ice458/RPN_Scientific_Calc/src/packs/PIC32CM2532LE00048_DFP/component/port.h

/*
 * Component description for PORT
 *
 * Copyright (c) 2023 Microchip Technology Inc. and its subsidiaries.
 *
 * Subject to your compliance with these terms, you may use Microchip software and any derivatives
 * exclusively with Microchip products. It is your responsibility to comply with third party license
 * terms applicable to your use of third party software (including open source software) that may
 * accompany Microchip software.
 *
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
 * IN NO EVENT WILL MICROCHIP BE LIABLE FOR ANY INDIRECT, SPECIAL, PUNITIVE, INCIDENTAL OR CONSEQUENTIAL
 * LOSS, DAMAGE, COST OR EXPENSE OF ANY KIND WHATSOEVER RELATED TO THE SOFTWARE, HOWEVER CAUSED, EVEN IF
 * MICROCHIP HAS BEEN ADVISED OF THE POSSIBILITY OR THE DAMAGES ARE FORESEEABLE. TO THE FULLEST EXTENT
 * ALLOWED BY LAW, MICROCHIP'S TOTAL LIABILITY ON ALL CLAIMS IN ANY WAY RELATED TO THIS SOFTWARE WILL NOT
 * EXCEED THE AMOUNT OF FEES, IF ANY, THAT YOU HAVE PAID DIRECTLY TO MICROCHIP FOR THIS SOFTWARE.
 *
 */

/* file generated from device description version 2022-09-09T06:08:26Z */
#ifndef _PIC32CMLE00_PORT_COMPONENT_H_
#define _PIC32CMLE00_PORT_COMPONENT_H_

/* ************************************************************************** */
/*   SOFTWARE API DEFINITION FOR PORT                                         */
/* ************************************************************************** */

/* -------- PORT_DIR : (PORT Offset: 0x00) (R/W 32) Data Direction -------- */
#define PORT_DIR_RESETVALUE                   _UINT32_(0x00)                                       /*  (PORT_DIR) Data Direction  Reset Value */

#define PORT_DIR_DIR_Pos                      _UINT32_(0)                                          /* (PORT_DIR) Port Data Direction Position */
#define PORT_DIR_DIR_Msk                      (_UINT32_(0xFFFFFFFF) << PORT_DIR_DIR_Pos)           /* (PORT_DIR) Port Data Direction Mask */
#define PORT_DIR_DIR(value)                   (PORT_DIR_DIR_Msk & (_UINT32_(value) << PORT_DIR_DIR_Pos)) /* Assigment of value for DIR in the PORT_DIR register */
#define PORT_DIR_Msk                          _UINT32_(0xFFFFFFFF)                                 /* (PORT_DIR) Register Mask  */


/* -------- PORT_DIRCLR : (PORT Offset: 0x04) (R/W 32) Data Direction Clear -------- */
#define PORT_DIRCLR_RESETVALUE                _UINT32_(0x00)                                       /*  (PORT_DIRCLR) Data Direction Clear  Reset Value */

#define PORT_DIRCLR_DIRCLR_Pos                _UINT32_(0)                                          /* (PORT_DIRCLR) Port Data Direction Clear Position */
#define PORT_DIRCLR_DIRCLR_Msk                (_UINT32_(0xFFFFFFFF) << PORT_DIRCLR_DIRCLR_Pos)     /* (PORT_DIRCLR) Port Data Direction Clear Mask */
#define PORT_DIRCLR_DIRCLR(value)             (PORT_DIRCLR_DIRCLR_Msk & (_UINT32_(value) << PORT_DIRCLR_DIRCLR_Pos)) /* Assigment of value for DIRCLR in the PORT_DIRCLR register */
#define PORT_DIRCLR_Msk                       _UINT32_(0xFFFFFFFF)                                 /* (PORT_DIRCLR) Register Mask  */


/* -------- PORT_DIRSET : (PORT Offset: 0x08) (R/W 32) Data Direction Set -------- */
#define PORT_DIRSET_RESETVALUE                _UINT32_(0x00)                                       /*  (PORT_DIRSET) Data Direction Set  Reset Value */

#define PORT_DIRSET_DIRSET_Pos                _UINT32_(0)                                          /* (PORT_DIRSET) Port Data Direction Set Position */
#define PORT_DIRSET_DIRSET_Msk                (_UINT32_(0xFFFFFFFF) << PORT_DIRSET_DIRSET_Pos)     /* (PORT_DIRSET) Port Data Direction Set Mask */
#define PORT_DIRSET_DIRSET(value)             (PORT_DIRSET_DIRSET_Msk & (_UINT32_(value) << PORT_DIRSET_DIRSET_Pos)) /* Assigment of value for DIRSET in the PORT_DIRSET register */
#define PORT_DIRSET_Msk                       _UINT32_(0xFFFFFFFF)                                 /* (PORT_DIRSET) Register Mask  */


/* -------- PORT_DIRTGL : (PORT Offset: 0x0C) (R/W 32) Data Direction Toggle -------- */
#define PORT_DIRTGL_RESETVALUE                _UINT32_(0x00)                                       /*  (PORT_DIRTGL) Data Direction Toggle  Reset Value */

#define PORT_DIRTGL_DIRTGL_Pos                _UINT32_(0)                                          /* (PORT_DIRTGL) Port Data Direction Toggle Position */
#define PORT_DIRTGL_DIRTGL_Msk                (_UINT32_(0xFFFFFFFF) << PORT_DIRTGL_DIRTGL_Pos)     /* (PORT_DIRTGL) Port Data Direction Toggle Mask */
#define PORT_DIRTGL_DIRTGL(value)             (PORT_DIRTGL_DIRTGL_Msk & (_UINT32_(value) << PORT_DIRTGL_DIRTGL_Pos)) /* Assigment of value for DIRTGL in the PORT_DIRTGL register */
#define PORT_DIRTGL_Msk                       _UINT32_(0xFFFFFFFF)                                 /* (PORT_DIRTGL) Register Mask  */


/* -------- PORT_OUT : (PORT Offset: 0x10) (R/W 32) Data Output Value -------- */
#define PORT_OUT_RESETVALUE                   _UINT32_(0x00)                                       /*  (PORT_OUT) Data Output Value  Reset Value */

#define PORT_OUT_OUT_Pos                      _UINT32_(0)                                          /* (PORT_OUT) PORT Data Output Value Position */
#define PORT_OUT_OUT_Msk                      (_UINT32_(0xFFFFFFFF) << PORT_OUT_OUT_Pos)           /* (PORT_OUT) PORT Data Output Value Mask */
#define PORT_OUT_OUT(value)                   (PORT_OUT_OUT_Msk & (_UINT32_(value) << PORT_OUT_OUT_Pos)) /* Assigment of value for OUT in the PORT_OUT register */
#define PORT_OUT_Msk                          _UINT32_(0xFFFFFFFF)                                 /* (PORT_OUT) Register Mask  */


/* -------- PORT_OUTCLR : (PORT Offset: 0x14) (R/W 32) Data Output Value Clear -------- */
#define PORT_OUTCLR_RESETVALUE                _UINT32_(0x00)                                       /*  (PORT_OUTCLR) Data Output Value Clear  Reset Value */

#define PORT_OUTCLR_OUTCLR_Pos                _UINT32_(0)                                          /* (PORT_OUTCLR) PORT Data Output Value Clear Position */
#define PORT_OUTCLR_OUTCLR_Msk                (_UINT32_(0xFFFFFFFF) << PORT_OUTCLR_OUTCLR_Pos)     /* (PORT_OUTCLR) PORT Data Output Value Clear Mask */
#define PORT_OUTCLR_OUTCLR(value)             (PORT_OUTCLR_OUTCLR_Msk & (_UINT32_(value) << PORT_OUTCLR_OUTCLR_Pos)) /* Assigment of value for OUTCLR in the PORT_OUTCLR register */
#define PORT_OUTCLR_Msk                       _UINT32_(0xFFFFFFFF)                                 /* (PORT_OUTCLR) Register Mask  */


/* -------- PORT_OUTSET : (PORT Offset: 0x18) (R/W 32) Data Output Value Set -------- */
#define PORT_OUTSET_RESETVALUE                _UINT32_(0x00)                                       /*  (PORT_OUTSET) Data Output Value Set  Reset Value */

#define PORT_OUTSET_OUTSET_Pos                _UINT32_(0)                                          /* (PORT_OUTSET) PORT Data Output Value Set Position */
#define PORT_OUTSET_OUTSET_Msk                (_UINT32_(0xFFFFFFFF) << PORT_OUTSET_OUTSET_Pos)     /* (PORT_OUTSET) PORT Data Output Value Set Mask */
#define PORT_OUTSET_OUTSET(value)             (PORT_OUTSET_OUTSET_Msk & (_UINT32_(value) << PORT_OUTSET_OUTSET_Pos)) /* Assigment of value for OUTSET in the PORT_OUTSET register */
#define PORT_OUTSET_Msk                       _UINT32_(0xFFFFFFFF)                                 /* (PORT_OUTSET) Register Mask  */


/* -------- PORT_OUTTGL : (PORT Offset: 0x1C) (R/W 32) Data Output Value Toggle -------- */
#define PORT_OUTTGL_RESETVALUE                _UINT32_(0x00)                                       /*  (PORT_OUTTGL) Data Output Value Toggle  Reset Value */

#define PORT_OUTTGL_OUTTGL_Pos                _UINT32_(0)                                          /* (PORT_OUTTGL) PORT Data Output Value Toggle Position */
#define PORT_OUTTGL_OUTTGL_Msk                (_UINT32_(0xFFFFFFFF) << PORT_OUTTGL_OUTTGL_Pos)     /* (PORT_OUTTGL) PORT Data Output Value Toggle Mask */
#define PORT_OUTTGL_OUTTGL(value)             (PORT_OUTTGL_OUTTGL_Msk & (_UINT32_(value) << PORT_OUTTGL_OUTTGL_Pos)) /* Assigment of value for OUTTGL in the PORT_OUTTGL register */
#define PORT_OUTTGL_Msk                       _UINT32_(0xFFFFFFFF)                                 /* (PORT_OUTTGL) Register Mask  */


/* -------- PORT_IN : (PORT Offset: 0x20) ( R/ 32) Data Input Value -------- */
#define PORT_IN_RESETVALUE                    _UINT32_(0x00)                                       /*  (PORT_IN) Data Input Value  Reset Value */

#define PORT_IN_IN_Pos                        _UINT32_(0)                                          /* (PORT_IN) PORT Data Input Value Position */
#define PORT_IN_IN_Msk                        (_UINT32_(0xFFFFFFFF) << PORT_IN_IN_Pos)             /* (PORT_IN) PORT Data Input Value Mask */
#define PORT_IN_IN(value)                     (PORT_IN_IN_Msk & (_UINT32_(value) << PORT_IN_IN_Pos)) /* Assigment of value for IN in the PORT_IN register */
#define PORT_IN_Msk                           _UINT32_(0xFFFFFFFF)                                 /* (PORT_IN) Register Mask  */


/* -------- PORT_CTRL : (PORT Offset: 0x24) (R/W 32) Control -------- */
#define PORT_CTRL_RESETVALUE                  _UINT32_(0x00)                                       /*  (PORT_CTRL) Control  Reset Value */

#define PORT_CTRL_SAMPLING_Pos                _UINT32_(0)                                          /* (PORT_CTRL) Input Sampling Mode Position */
#define PORT_CTRL_SAMPLING_Msk                (_UINT32_(0xFFFFFFFF) << PORT_CTRL_SAMPLING_Pos)     /* (PORT_CTRL) Input Sampling Mode Mask */
#define PORT_CTRL_SAMPLING(value)             (PORT_CTRL_SAMPLING_Msk & (_UINT32_(value) << PORT_CTRL_SAMPLING_Pos)) /* Assigment of value for SAMPLING in the PORT_CTRL register */
#define PORT_CTRL_Msk                         _UINT32_(0xFFFFFFFF)                                 /* (PORT_CTRL) Register Mask  */


/* -------- PORT_WRCONFIG : (PORT Offset: 0x28) ( /W 32) Write Configuration -------- */
#define PORT_WRCONFIG_RESETVALUE              _UINT32_(0x00)                                       /*  (PORT_WRCONFIG) Write Configuration  Reset Value */

#define PORT_WRCONFIG_PINMASK_Pos             _UINT32_(0)                                          /* (PORT_WRCONFIG) Pin Mask for Multiple Pin Configuration Position */
#define PORT_WRCONFIG_PINMASK_Msk             (_UINT32_(0xFFFF) << PORT_WRCONFIG_PINMASK_Pos)      /* (PORT_WRCONFIG) Pin Mask for Multiple Pin Configuration Mask */
#define PORT_WRCONFIG_PINMASK(value)          (PORT_WRCONFIG_PINMASK_Msk & (_UINT32_(value) << PORT_WRCONFIG_PINMASK_Pos)) /* Assigment of value for PINMASK in the PORT_WRCONFIG register */
#define PORT_WRCONFIG_PMUXEN_Pos              _UINT32_(16)                                         /* (PORT_WRCONFIG) Peripheral Multiplexer Enable Position */
#define PORT_WRCONFIG_PMUXEN_Msk              (_UINT32_(0x1) << PORT_WRCONFIG_PMUXEN_Pos)          /* (PORT_WRCONFIG) Peripheral Multiplexer Enable Mask */
#define PORT_WRCONFIG_PMUXEN(value)           (PORT_WRCONFIG_PMUXEN_Msk & (_UINT32_(value) << PORT_WRCONFIG_PMUXEN_Pos)) /* Assigment of value for PMUXEN in the PORT_WRCONFIG register */
#define PORT_WRCONFIG_INEN_Pos                _UINT32_(17)                                         /* (PORT_WRCONFIG) Input Enable Position */
#define PORT_WRCONFIG_INEN_Msk                (_UINT32_(0x1) << PORT_WRCONFIG_INEN_Pos)            /* (PORT_WRCONFIG) Input Enable Mask */
#define PORT_WRCONFIG_INEN(value)             (PORT_WRCONFIG_INEN_Msk & (_UINT32_(value) << PORT_WRCONFIG_INEN_Pos)) /* Assigment of value for INEN in the PORT_WRCONFIG register */
#define PORT_WRCONFIG_PULLEN_Pos              _UINT32_(18)                                         /* (PORT_WRCONFIG) Pull Enable Position */
#define PORT_WRCONFIG_PULLEN_Msk              (_UINT32_(0x1) << PORT_WRCONFIG_PULLEN_Pos)          /* (PORT_WRCONFIG) Pull Enable Mask */
#define PORT_WRCONFIG_PULLEN(value)           (PORT_WRCONFIG_PULLEN_Msk & (_UINT32_(value) << PORT_WRCONFIG_PULLEN_Pos)) /* Assigment of value for PULLEN in the PORT_WRCONFIG register */
#define PORT_WRCONFIG_DRVSTR_Pos              _UINT32_(22)                                         /* (PORT_WRCONFIG) Output Driver Strength Selection Position */
#define PORT_WRCONFIG_DRVSTR_Msk              (_UINT32_(0x1) << PORT_WRCONFIG_DRVSTR_Pos)          /* (PORT_WRCONFIG) Output Driver Strength Selection Mask */
#define PORT_WRCONFIG_DRVSTR(value)           (PORT_WRCONFIG_DRVSTR_Msk & (_UINT32_(value) << PORT_WRCONFIG_DRVSTR_Pos)) /* Assigment of value for DRVSTR in the PORT_WRCONFIG register */
#define PORT_WRCONFIG_PMUX_Pos                _UINT32_(24)                                         /* (PORT_WRCONFIG) Peripheral Multiplexing Position */
#define PORT_WRCONFIG_PMUX_Msk                (_UINT32_(0xF) << PORT_WRCONFIG_PMUX_Pos)            /* (PORT_WRCONFIG) Peripheral Multiplexing Mask */
#define PORT_WRCONFIG_PMUX(value)             (PORT_WRCONFIG_PMUX_Msk & (_UINT32_(value) << PORT_WRCONFIG_PMUX_Pos)) /* Assigment of value for PMUX in the PORT_WRCONFIG register */
#define PORT_WRCONFIG_WRPMUX_Pos              _UINT32_(28)                                         /* (PORT_WRCONFIG) Write PMUX Position */
#define PORT_WRCONFIG_WRPMUX_Msk              (_UINT32_(0x1) << PORT_WRCONFIG_WRPMUX_Pos)          /* (PORT_WRCONFIG) Write PMUX Mask */
#define PORT_WRCONFIG_WRPMUX(value)           (PORT_WRCONFIG_WRPMUX_Msk & (_UINT32_(value) << PORT_WRCONFIG_WRPMUX_Pos)) /* Assigment of value for WRPMUX in the PORT_WRCONFIG register */
#define PORT_WRCONFIG_WRPINCFG_Pos            _UINT32_(30)                                         /* (PORT_WRCONFIG) Write PINCFG Position */
#define PORT_WRCONFIG_WRPINCFG_Msk            (_UINT32_(0x1) << PORT_WRCONFIG_WRPINCFG_Pos)        /* (PORT_WRCONFIG) Write PINCFG Mask */
#define PORT_WRCONFIG_WRPINCFG(value)         (PORT_WRCONFIG_WRPINCFG_Msk & (_UINT32_(value) << PORT_WRCONFIG_WRPINCFG_Pos)) /* Assigment of value for WRPINCFG in the PORT_WRCONFIG register */
#define PORT_WRCONFIG_HWSEL_Pos               _UINT32_(31)                                         /* (PORT_WRCONFIG) Half-Word Select Position */
#define PORT_WRCONFIG_HWSEL_Msk               (_UINT32_(0x1) << PORT_WRCONFIG_HWSEL_Pos)           /* (PORT_WRCONFIG) Half-Word Select Mask */
#define PORT_WRCONFIG_HWSEL(value)            (PORT_WRCONFIG_HWSEL_Msk & (_UINT32_(value) << PORT_WRCONFIG_HWSEL_Pos)) /* Assigment of value for HWSEL in the PORT_WRCONFIG register */
#define PORT_WRCONFIG_Msk                     _UINT32_(0xDF47FFFF)                                 /* (PORT_WRCONFIG) Register Mask  */


/* -------- PORT_EVCTRL : (PORT Offset: 0x2C) (R/W 32) Event Input Control -------- */
#define PORT_EVCTRL_RESETVALUE                _UINT32_(0x00)                                       /*  (PORT_EVCTRL) Event Input Control  Reset Value */

#define PORT_EVCTRL_PID0_Pos                  _UINT32_(0)                                          /* (PORT_EVCTRL) PORT Event Pin Identifier 0 Position */
#define PORT_EVCTRL_PID0_Msk                  (_UINT32_(0x1F) << PORT_EVCTRL_PID0_Pos)             /* (PORT_EVCTRL) PORT Event Pin Identifier 0 Mask */
#define PORT_EVCTRL_PID0(value)               (PORT_EVCTRL_PID0_Msk & (_UINT32_(value) << PORT_EVCTRL_PID0_Pos)) /* Assigment of value for PID0 in the PORT_EVCTRL register */
#define PORT_EVCTRL_EVACT0_Pos                _UINT32_(5)                                          /* (PORT_EVCTRL) PORT Event Action 0 Position */
#define PORT_EVCTRL_EVACT0_Msk                (_UINT32_(0x3) << PORT_EVCTRL_EVACT0_Pos)            /* (PORT_EVCTRL) PORT Event Action 0 Mask */
#define PORT_EVCTRL_EVACT0(value)             (PORT_EVCTRL_EVACT0_Msk & (_UINT32_(value) << PORT_EVCTRL_EVACT0_Pos)) /* Assigment of value for EVACT0 in the PORT_EVCTRL register */
#define   PORT_EVCTRL_EVACT0_OUT_Val          _UINT32_(0x0)                                        /* (PORT_EVCTRL) Event output to pin  */
#define   PORT_EVCTRL_EVACT0_SET_Val          _UINT32_(0x1)                                        /* (PORT_EVCTRL) Set output register of pin on event  */
#define   PORT_EVCTRL_EVACT0_CLR_Val          _UINT32_(0x2)                                        /* (PORT_EVCTRL) Clear output register of pin on event  */
#define   PORT_EVCTRL_EVACT0_TGL_Val          _UINT32_(0x3)                                        /* (PORT_EVCTRL) Toggle output register of pin on event  */
#define PORT_EVCTRL_EVACT0_OUT                (PORT_EVCTRL_EVACT0_OUT_Val << PORT_EVCTRL_EVACT0_Pos) /* (PORT_EVCTRL) Event output to pin Position  */
#define PORT_EVCTRL_EVACT0_SET                (PORT_EVCTRL_EVACT0_SET_Val << PORT_EVCTRL_EVACT0_Pos) /* (PORT_EVCTRL) Set output register of pin on event Position  */
#define PORT_EVCTRL_EVACT0_CLR                (PORT_EVCTRL_EVACT0_CLR_Val << PORT_EVCTRL_EVACT0_Pos) /* (PORT_EVCTRL) Clear output register of pin on event Position  */
#define PORT_EVCTRL_EVACT0_TGL                (PORT_EVCTRL_EVACT0_TGL_Val << PORT_EVCTRL_EVACT0_Pos) /* (PORT_EVCTRL) Toggle output register of pin on event Position  */
#define PORT_EVCTRL_PORTEI0_Pos               _UINT32_(7)                                          /* (PORT_EVCTRL) PORT Event Input Enable 0 Position */
#define PORT_EVCTRL_PORTEI0_Msk               (_UINT32_(0x1) << PORT_EVCTRL_PORTEI0_Pos)           /* (PORT_EVCTRL) PORT Event Input Enable 0 Mask */
#define PORT_EVCTRL_PORTEI0(value)            (PORT_EVCTRL_PORTEI0_Msk & (_UINT32_(value) << PORT_EVCTRL_PORTEI0_Pos)) /* Assigment of value for PORTEI0 in the PORT_EVCTRL register */
#define PORT_EVCTRL_PID1_Pos                  _UINT32_(8)                                          /* (PORT_EVCTRL) PORT Event Pin Identifier 1 Position */
#define PORT_EVCTRL_PID1_Msk                  (_UINT32_(0x1F) << PORT_EVCTRL_PID1_Pos)             /* (PORT_EVCTRL) PORT Event Pin Identifier 1 Mask */
#define PORT_EVCTRL_PID1(value)               (PORT_EVCTRL_PID1_Msk & (_UINT32_(value) << PORT_EVCTRL_PID1_Pos)) /* Assigment of value for PID1 in the PORT_EVCTRL register */
#define PORT_EVCTRL_EVACT1_Pos                _UINT32_(13)                                         /* (PORT_EVCTRL) PORT Event Action 1 Position */
#define PORT_EVCTRL_EVACT1_Msk                (_UINT32_(0x3) << PORT_EVCTRL_EVACT1_Pos)            /* (PORT_EVCTRL) PORT Event Action 1 Mask */
#define PORT_EVCTRL_EVACT1(value)             (PORT_EVCTRL_EVACT1_Msk & (_UINT32_(value) << PORT_EVCTRL_EVACT1_Pos)) /* Assigment of value for EVACT1 in the PORT_EVCTRL register */
#define PORT_EVCTRL_PORTEI1_Pos               _UINT32_(15)                                         /* (PORT_EVCTRL) PORT Event Input Enable 1 Position */
#define PORT_EVCTRL_PORTEI1_Msk               (_UINT32_(0x1) << PORT_EVCTRL_PORTEI1_Pos)           /* (PORT_EVCTRL) PORT Event Input Enable 1 Mask */
#define PORT_EVCTRL_PORTEI1(value)            (PORT_EVCTRL_PORTEI1_Msk & (_UINT32_(value) << PORT_EVCTRL_PORTEI1_Pos)) /* Assigment of value for PORTEI1 in the PORT_EVCTRL register */
#define PORT_EVCTRL_PID2_Pos                  _UINT32_(16)                                         /* (PORT_EVCTRL) PORT Event Pin Identifier 2 Position */
#define PORT_EVCTRL_PID2_Msk                  (_UINT32_(0x1F) << PORT_EVCTRL_PID2_Pos)             /* (PORT_EVCTRL) PORT Event Pin Identifier 2 Mask */
#define PORT_EVCTRL_PID2(value)               (PORT_EVCTRL_PID2_Msk & (_UINT32_(value) << PORT_EVCTRL_PID2_Pos)) /* Assigment of value for PID2 in the PORT_EVCTRL register */
#define PORT_EVCTRL_EVACT2_Pos                _UINT32_(21)                                         /* (PORT_EVCTRL) PORT Event Action 2 Position */
#define PORT_EVCTRL_EVACT2_Msk                (_UINT32_(0x3) << PORT_EVCTRL_EVACT2_Pos)            /* (PORT_EVCTRL) PORT Event Action 2 Mask */
#define PORT_EVCTRL_EVACT2(value)             (PORT_EVCTRL_EVACT2_Msk & (_UINT32_(value) << PORT_EVCTRL_EVACT2_Pos)) /* Assigment of value for EVACT2 in the PORT_EVCTRL register */
#define PORT_EVCTRL_PORTEI2_Pos               _UINT32_(23)                                         /* (PORT_EVCTRL) PORT Event Input Enable 2 Position */
#define PORT_EVCTRL_PORTEI2_Msk               (_UINT32_(0x1) << PORT_EVCTRL_PORTEI2_Pos)           /* (PORT_EVCTRL) PORT Event Input Enable 2 Mask */
#define PORT_EVCTRL_PORTEI2(value)            (PORT_EVCTRL_PORTEI2_Msk & (_UINT32_(value) << PORT_EVCTRL_PORTEI2_Pos)) /* Assigment of value for PORTEI2 in the PORT_EVCTRL register */
#define PORT_EVCTRL_PID3_Pos                  _UINT32_(24)                                         /* (PORT_EVCTRL) PORT Event Pin Identifier 3 Position */
#define PORT_EVCTRL_PID3_Msk                  (_UINT32_(0x1F) << PORT_EVCTRL_PID3_Pos)             /* (PORT_EVCTRL) PORT Event Pin Identifier 3 Mask */
#define PORT_EVCTRL_PID3(value)               (PORT_EVCTRL_PID3_Msk & (_UINT32_(value) << PORT_EVCTRL_PID3_Pos)) /* Assigment of value for PID3 in the PORT_EVCTRL register */
#define PORT_EVCTRL_EVACT3_Pos                _UINT32_(29)                                         /* (PORT_EVCTRL) PORT Event Action 3 Position */
#define PORT_EVCTRL_EVACT3_Msk                (_UINT32_(0x3) << PORT_EVCTRL_EVACT3_Pos)            /* (PORT_EVCTRL) PORT Event Action 3 Mask */
#define PORT_EVCTRL_EVACT3(value)             (PORT_EVCTRL_EVACT3_Msk & (_UINT32_(value) << PORT_EVCTRL_EVACT3_Pos)) /* Assigment of value for EVACT3 in the PORT_EVCTRL register */
#define PORT_EVCTRL_PORTEI3_Pos               _UINT32_(31)                                         /* (PORT_EVCTRL) PORT Event Input Enable 3 Position */
#define PORT_EVCTRL_PORTEI3_Msk               (_UINT32_(0x1) << PORT_EVCTRL_PORTEI3_Pos)           /* (PORT_EVCTRL) PORT Event Input Enable 3 Mask */
#define PORT_EVCTRL_PORTEI3(value)            (PORT_EVCTRL_PORTEI3_Msk & (_UINT32_(value) << PORT_EVCTRL_PORTEI3_Pos)) /* Assigment of value for PORTEI3 in the PORT_EVCTRL register */
#define PORT_EVCTRL_Msk                       _UINT32_(0xFFFFFFFF)                                 /* (PORT_EVCTRL) Register Mask  */


/* -------- PORT_PMUX : (PORT Offset: 0x30) (R/W 8) Peripheral Multiplexing -------- */
#define PORT_PMUX_RESETVALUE                  _UINT8_(0x00)                                        /*  (PORT_PMUX) Peripheral Multiplexing  Reset Value */

#define PORT_PMUX_PMUXE_Pos                   _UINT8_(0)                                           /* (PORT_PMUX) Peripheral Multiplexing for Even-Numbered Pin Position */
#define PORT_PMUX_PMUXE_Msk                   (_UINT8_(0xF) << PORT_PMUX_PMUXE_Pos)                /* (PORT_PMUX) Peripheral Multiplexing for Even-Numbered Pin Mask */
#define PORT_PMUX_PMUXE(value)                (PORT_PMUX_PMUXE_Msk & (_UINT8_(value) << PORT_PMUX_PMUXE_Pos)) /* Assigment of value for PMUXE in the PORT_PMUX register */
#define   PORT_PMUX_PMUXE_A_Val               _UINT8_(0x0)                                         /* (PORT_PMUX) Peripheral function A selected  */
#define   PORT_PMUX_PMUXE_B_Val               _UINT8_(0x1)                                         /* (PORT_PMUX) Peripheral function B selected  */
#define   PORT_PMUX_PMUXE_C_Val               _UINT8_(0x2)                                         /* (PORT_PMUX) Peripheral function C selected  */
#define   PORT_PMUX_PMUXE_D_Val               _UINT8_(0x3)                                         /* (PORT_PMUX) Peripheral function D selected  */
#define   PORT_PMUX_PMUXE_E_Val               _UINT8_(0x4)                                         /* (PORT_PMUX) Peripheral function E selected  */
#define   PORT_PMUX_PMUXE_G_Val               _UINT8_(0x6)                                         /* (PORT_PMUX) Peripheral function G selected  */
#define   PORT_PMUX_PMUXE_H_Val               _UINT8_(0x7)                                         /* (PORT_PMUX) Peripheral function H selected  */
#define   PORT_PMUX_PMUXE_I_Val               _UINT8_(0x8)                                         /* (PORT_PMUX) Peripheral function I selected  */
#define   PORT_PMUX_PMUXE_J_Val               _UINT8_(0x9)                                         /* (PORT_PMUX) Peripheral function J selected  */
#define   PORT_PMUX_PMUXE_K_Val               _UINT8_(0xA)                                         /* (PORT_PMUX) Peripheral function K selected  */
#define PORT_PMUX_PMUXE_A                     (PORT_PMUX_PMUXE_A_Val << PORT_PMUX_PMUXE_Pos)       /* (PORT_PMUX) Peripheral function A selected Position  */
#define PORT_PMUX_PMUXE_B                     (PORT_PMUX_PMUXE_B_Val << PORT_PMUX_PMUXE_Pos)       /* (PORT_PMUX) Peripheral function B selected Position  */
#define PORT_PMUX_PMUXE_C                     (PORT_PMUX_PMUXE_C_Val << PORT_PMUX_PMUXE_Pos)       /* (PORT_PMUX) Peripheral function C selected Position  */
#define PORT_PMUX_PMUXE_D                     (PORT_PMUX_PMUXE_D_Val << PORT_PMUX_PMUXE_Pos)       /* (PORT_PMUX) Peripheral function D selected Position  */
#define PORT_PMUX_PMUXE_E                     (PORT_PMUX_PMUXE_E_Val << PORT_PMUX_PMUXE_Pos)       /* (PORT_PMUX) Peripheral function E selected Position  */
#define PORT_PMUX_PMUXE_G                     (PORT_PMUX_PMUXE_G_Val << PORT_PMUX_PMUXE_Pos)       /* (PORT_PMUX) Peripheral function G selected Position  */
#define PORT_PMUX_PMUXE_H                     (PORT_PMUX_PMUXE_H_Val << PORT_PMUX_PMUXE_Pos)       /* (PORT_PMUX) Peripheral function H selected Position  */
#define PORT_PMUX_PMUXE_I                     (PORT_PMUX_PMUXE_I_Val << PORT_PMUX_PMUXE_Pos)       /* (PORT_PMUX) Peripheral function I selected Position  */
#define PORT_PMUX_PMUXE_J                     (PORT_PMUX_PMUXE_J_Val << PORT_PMUX_PMUXE_Pos)       /* (PORT_PMUX) Peripheral function J selected Position  */
#define PORT_PMUX_PMUXE_K                     (PORT_PMUX_PMUXE_K_Val << PORT_PMUX_PMUXE_Pos)       /* (PORT_PMUX) Peripheral function K selected Position  */
#define PORT_PMUX_PMUXO_Pos                   _UINT8_(4)                                           /* (PORT_PMUX) Peripheral Multiplexing for Odd-Numbered Pin Position */
#define PORT_PMUX_PMUXO_Msk                   (_UINT8_(0xF) << PORT_PMUX_PMUXO_Pos)                /* (PORT_PMUX) Peripheral Multiplexing for Odd-Numbered Pin Mask */
#define PORT_PMUX_PMUXO(value)                (PORT_PMUX_PMUXO_Msk & (_UINT8_(value) << PORT_PMUX_PMUXO_Pos)) /* Assigment of value for PMUXO in the PORT_PMUX register */
#define   PORT_PMUX_PMUXO_A_Val               _UINT8_(0x0)                                         /* (PORT_PMUX) Peripheral function A selected  */
#define   PORT_PMUX_PMUXO_B_Val               _UINT8_(0x1)                                         /* (PORT_PMUX) Peripheral function B selected  */
#define   PORT_PMUX_PMUXO_C_Val               _UINT8_(0x2)                                         /* (PORT_PMUX) Peripheral function C selected  */
#define   PORT_PMUX_PMUXO_D_Val               _UINT8_(0x3)                                         /* (PORT_PMUX) Peripheral function D selected  */
#define   PORT_PMUX_PMUXO_E_Val               _UINT8_(0x4)                                         /* (PORT_PMUX) Peripheral function E selected  */
#define   PORT_PMUX_PMUXO_G_Val               _UINT8_(0x6)                                         /* (PORT_PMUX) Peripheral function G selected  */
#define   PORT_PMUX_PMUXO_H_Val               _UINT8_(0x7)                                         /* (PORT_PMUX) Peripheral function H selected  */
#define   PORT_PMUX_PMUXO_I_Val               _UINT8_(0x8)                                         /* (PORT_PMUX) Peripheral function I selected  */
#define   PORT_PMUX_PMUXO_J_Val               _UINT8_(0x9)                                         /* (PORT_PMUX) Peripheral function J selected  */
#define   PORT_PMUX_PMUXO_K_Val               _UINT8_(0xA)                                         /* (PORT_PMUX) Peripheral function K selected  */
#define PORT_PMUX_PMUXO_A                     (PORT_PMUX_PMUXO_A_Val << PORT_PMUX_PMUXO_Pos)       /* (PORT_PMUX) Peripheral function A selected Position  */
#define PORT_PMUX_PMUXO_B                     (PORT_PMUX_PMUXO_B_Val << PORT_PMUX_PMUXO_Pos)       /* (PORT_PMUX) Peripheral function B selected Position  */
#define PORT_PMUX_PMUXO_C                     (PORT_PMUX_PMUXO_C_Val << PORT_PMUX_PMUXO_Pos)       /* (PORT_PMUX) Peripheral function C selected Position  */
#define PORT_PMUX_PMUXO_D                     (PORT_PMUX_PMUXO_D_Val << PORT_PMUX_PMUXO_Pos)       /* (PORT_PMUX) Peripheral function D selected Position  */
#define PORT_PMUX_PMUXO_E                     (PORT_PMUX_PMUXO_E_Val << PORT_PMUX_PMUXO_Pos)       /* (PORT_PMUX) Peripheral function E selected Position  */
#define PORT_PMUX_PMUXO_G                     (PORT_PMUX_PMUXO_G_Val << PORT_PMUX_PMUXO_Pos)       /* (PORT_PMUX) Peripheral function G selected Position  */
#define PORT_PMUX_PMUXO_H                     (PORT_PMUX_PMUXO_H_Val << PORT_PMUX_PMUXO_Pos)       /* (PORT_PMUX) Peripheral function H selected Position  */
#define PORT_PMUX_PMUXO_I                     (PORT_PMUX_PMUXO_I_Val << PORT_PMUX_PMUXO_Pos)       /* (PORT_PMUX) Peripheral function I selected Position  */
#define PORT_PMUX_PMUXO_J                     (PORT_PMUX_PMUXO_J_Val << PORT_PMUX_PMUXO_Pos)       /* (PORT_PMUX) Peripheral function J selected Position  */
#define PORT_PMUX_PMUXO_K                     (PORT_PMUX_PMUXO_K_Val << PORT_PMUX_PMUXO_Pos)       /* (PORT_PMUX) Peripheral function K selected Position  */
#define PORT_PMUX_Msk                         _UINT8_(0xFF)                                        /* (PORT_PMUX) Register Mask  */


/* -------- PORT_PINCFG : (PORT Offset: 0x40) (R/W 8) Pin Configuration -------- */
#define PORT_PINCFG_RESETVALUE                _UINT8_(0x00)                                        /*  (PORT_PINCFG) Pin Configuration  Reset Value */

#define PORT_PINCFG_PMUXEN_Pos                _UINT8_(0)                                           /* (PORT_PINCFG) Peripheral Multiplexer Enable Position */
#define PORT_PINCFG_PMUXEN_Msk                (_UINT8_(0x1) << PORT_PINCFG_PMUXEN_Pos)             /* (PORT_PINCFG) Peripheral Multiplexer Enable Mask */
#define PORT_PINCFG_PMUXEN(value)             (PORT_PINCFG_PMUXEN_Msk & (_UINT8_(value) << PORT_PINCFG_PMUXEN_Pos)) /* Assigment of value for PMUXEN in the PORT_PINCFG register */
#define PORT_PINCFG_INEN_Pos                  _UINT8_(1)                                           /* (PORT_PINCFG) Input Enable Position */
#define PORT_PINCFG_INEN_Msk                  (_UINT8_(0x1) << PORT_PINCFG_INEN_Pos)               /* (PORT_PINCFG) Input Enable Mask */
#define PORT_PINCFG_INEN(value)               (PORT_PINCFG_INEN_Msk & (_UINT8_(value) << PORT_PINCFG_INEN_Pos)) /* Assigment of value for INEN in the PORT_PINCFG register */
#define PORT_PINCFG_PULLEN_Pos                _UINT8_(2)                                           /* (PORT_PINCFG) Pull Enable Position */
#define PORT_PINCFG_PULLEN_Msk                (_UINT8_(0x1) << PORT_PINCFG_PULLEN_Pos)             /* (PORT_PINCFG) Pull Enable Mask */
#define PORT_PINCFG_PULLEN(value)             (PORT_PINCFG_PULLEN_Msk & (_UINT8_(value) << PORT_PINCFG_PULLEN_Pos)) /* Assigment of value for PULLEN in the PORT_PINCFG register */
#define PORT_PINCFG_DRVSTR_Pos                _UINT8_(6)                                           /* (PORT_PINCFG) Output Driver Strength Selection Position */
#define PORT_PINCFG_DRVSTR_Msk                (_UINT8_(0x1) << PORT_PINCFG_DRVSTR_Pos)             /* (PORT_PINCFG) Output Driver Strength Selection Mask */
#define PORT_PINCFG_DRVSTR(value)             (PORT_PINCFG_DRVSTR_Msk & (_UINT8_(value) << PORT_PINCFG_DRVSTR_Pos)) /* Assigment of value for DRVSTR in the PORT_PINCFG register */
#define PORT_PINCFG_Msk                       _UINT8_(0x47)                                        /* (PORT_PINCFG) Register Mask  */


/** \brief PORT register offsets definitions */
#define PORT_DIR_REG_OFST              _UINT32_(0x00)      /* (PORT_DIR) Data Direction Offset */
#define PORT_DIRCLR_REG_OFST           _UINT32_(0x04)      /* (PORT_DIRCLR) Data Direction Clear Offset */
#define PORT_DIRSET_REG_OFST           _UINT32_(0x08)      /* (PORT_DIRSET) Data Direction Set Offset */
#define PORT_DIRTGL_REG_OFST           _UINT32_(0x0C)      /* (PORT_DIRTGL) Data Direction Toggle Offset */
#define PORT_OUT_REG_OFST              _UINT32_(0x10)      /* (PORT_OUT) Data Output Value Offset */
#define PORT_OUTCLR_REG_OFST           _UINT32_(0x14)      /* (PORT_OUTCLR) Data Output Value Clear Offset */
#define PORT_OUTSET_REG_OFST           _UINT32_(0x18)      /* (PORT_OUTSET) Data Output Value Set Offset */
#define PORT_OUTTGL_REG_OFST           _UINT32_(0x1C)      /* (PORT_OUTTGL) Data Output Value Toggle Offset */
#define PORT_IN_REG_OFST               _UINT32_(0x20)      /* (PORT_IN) Data Input Value Offset */
#define PORT_CTRL_REG_OFST             _UINT32_(0x24)      /* (PORT_CTRL) Control Offset */
#define PORT_WRCONFIG_REG_OFST         _UINT32_(0x28)      /* (PORT_WRCONFIG) Write Configuration Offset */
#define PORT_EVCTRL_REG_OFST           _UINT32_(0x2C)      /* (PORT_EVCTRL) Event Input Control Offset */
#define PORT_PMUX_REG_OFST             _UINT32_(0x30)      /* (PORT_PMUX) Peripheral Multiplexing Offset */
#define PORT_PMUX0_REG_OFST            _UINT32_(0x30)      /* (PORT_PMUX0) Peripheral Multiplexing Offset */
#define PORT_PMUX1_REG_OFST            _UINT32_(0x31)      /* (PORT_PMUX1) Peripheral Multiplexing Offset */
#define PORT_PMUX2_REG_OFST            _UINT32_(0x32)      /* (PORT_PMUX2) Peripheral Multiplexing Offset */
#define PORT_PMUX3_REG_OFST            _UINT32_(0x33)      /* (PORT_PMUX3) Peripheral Multiplexing Offset */
#define PORT_PMUX4_REG_OFST            _UINT32_(0x34)      /* (PORT_PMUX4) Peripheral Multiplexing Offset */
#define PORT_PMUX5_REG_OFST            _UINT32_(0x35)      /* (PORT_PMUX5) Peripheral Multiplexing Offset */
#define PORT_PMUX6_REG_OFST            _UINT32_(0x36)      /* (PORT_PMUX6) Peripheral Multiplexing Offset */
#define PORT_PMUX7_REG_OFST            _UINT32_(0x37)      /* (PORT_PMUX7) Peripheral Multiplexing Offset */
#define PORT_PMUX8_REG_OFST            _UINT32_(0x38)      /* (PORT_PMUX8) Peripheral Multiplexing Offset */
#define PORT_PMUX9_REG_OFST            _UINT32_(0x39)      /* (PORT_PMUX9) Peripheral Multiplexing Offset */
#define PORT_PMUX10_REG_OFST           _UINT32_(0x3A)      /* (PORT_PMUX10) Peripheral Multiplexing Offset */
#define PORT_PMUX11_REG_OFST           _UINT32_(0x3B)      /* (PORT_PMUX11) Peripheral Multiplexing Offset */
#define PORT_PMUX12_REG_OFST           _UINT32_(0x3C)      /* (PORT_PMUX12) Peripheral Multiplexing Offset */
#define PORT_PMUX13_REG_OFST           _UINT32_(0x3D)      /* (PORT_PMUX13) Peripheral Multiplexing Offset */
#define PORT_PMUX14_REG_OFST           _UINT32_(0x3E)      /* (PORT_PMUX14) Peripheral Multiplexing Offset */
#define PORT_PMUX15_REG_OFST           _UINT32_(0x3F)      /* (PORT_PMUX15) Peripheral Multiplexing Offset */
#define PORT_PINCFG_REG_OFST           _UINT32_(0x40)      /* (PORT_PINCFG) Pin Configuration Offset */
#define PORT_PINCFG0_REG_OFST          _UINT32_(0x40)      /* (PORT_PINCFG0) Pin Configuration Offset */
#define PORT_PINCFG1_REG_OFST          _UINT32_(0x41)      /* (PORT_PINCFG1) Pin Configuration Offset */
#define PORT_PINCFG2_REG_OFST          _UINT32_(0x42)      /* (PORT_PINCFG2) Pin Configuration Offset */
#define PORT_PINCFG3_REG_OFST          _UINT32_(0x43)      /* (PORT_PINCFG3) Pin Configuration Offset */
#define PORT_PINCFG4_REG_OFST          _UINT32_(0x44)      /* (PORT_PINCFG4) Pin Configuration Offset */
#define PORT_PINCFG5_REG_OFST          _UINT32_(0x45)      /* (PORT_PINCFG5) Pin Configuration Offset */
#define PORT_PINCFG6_REG_OFST          _UINT32_(0x46)      /* (PORT_PINCFG6) Pin Configuration Offset */
#define PORT_PINCFG7_REG_OFST          _UINT32_(0x47)      /* (PORT_PINCFG7) Pin Configuration Offset */
#define PORT_PINCFG8_REG_OFST          _UINT32_(0x48)      /* (PORT_PINCFG8) Pin Configuration Offset */
#define PORT_PINCFG9_REG_OFST          _UINT32_(0x49)      /* (PORT_PINCFG9) Pin Configuration Offset */
#define PORT_PINCFG10_REG_OFST         _UINT32_(0x4A)      /* (PORT_PINCFG10) Pin Configuration Offset */
#define PORT_PINCFG11_REG_OFST         _UINT32_(0x4B)      /* (PORT_PINCFG11) Pin Configuration Offset */
#define PORT_PINCFG12_REG_OFST         _UINT32_(0x4C)      /* (PORT_PINCFG12) Pin Configuration Offset */
#define PORT_PINCFG13_REG_OFST         _UINT32_(0x4D)      /* (PORT_PINCFG13) Pin Configuration Offset */
#define PORT_PINCFG14_REG_OFST         _UINT32_(0x4E)      /* (PORT_PINCFG14) Pin Configuration Offset */
#define PORT_PINCFG15_REG_OFST         _UINT32_(0x4F)      /* (PORT_PINCFG15) Pin Configuration Offset */
#define PORT_PINCFG16_REG_OFST         _UINT32_(0x50)      /* (PORT_PINCFG16) Pin Configuration Offset */
#define PORT_PINCFG17_REG_OFST         _UINT32_(0x51)      /* (PORT_PINCFG17) Pin Configuration Offset */
#define PORT_PINCFG18_REG_OFST         _UINT32_(0x52)      /* (PORT_PINCFG18) Pin Configuration Offset */
#define PORT_PINCFG19_REG_OFST         _UINT32_(0x53)      /* (PORT_PINCFG19) Pin Configuration Offset */
#define PORT_PINCFG20_REG_OFST         _UINT32_(0x54)      /* (PORT_PINCFG20) Pin Configuration Offset */
#define PORT_PINCFG21_REG_OFST         _UINT32_(0x55)      /* (PORT_PINCFG21) Pin Configuration Offset */
#define PORT_PINCFG22_REG_OFST         _UINT32_(0x56)      /* (PORT_PINCFG22) Pin Configuration Offset */
#define PORT_PINCFG23_REG_OFST         _UINT32_(0x57)      /* (PORT_PINCFG23) Pin Configuration Offset */
#define PORT_PINCFG24_REG_OFST         _UINT32_(0x58)      /* (PORT_PINCFG24) Pin Configuration Offset */
#define PORT_PINCFG25_REG_OFST         _UINT32_(0x59)      /* (PORT_PINCFG25) Pin Configuration Offset */
#define PORT_PINCFG26_REG_OFST         _UINT32_(0x5A)      /* (PORT_PINCFG26) Pin Configuration Offset */
#define PORT_PINCFG27_REG_OFST         _UINT32_(0x5B)      /* (PORT_PINCFG27) Pin Configuration Offset */
#define PORT_PINCFG28_REG_OFST         _UINT32_(0x5C)      /* (PORT_PINCFG28) Pin Configuration Offset */
#define PORT_PINCFG29_REG_OFST         _UINT32_(0x5D)      /* (PORT_PINCFG29) Pin Configuration Offset */
#define PORT_PINCFG30_REG_OFST         _UINT32_(0x5E)      /* (PORT_PINCFG30) Pin Configuration Offset */
#define PORT_PINCFG31_REG_OFST         _UINT32_(0x5F)      /* (PORT_PINCFG31) Pin Configuration Offset */

#if !(defined(__ASSEMBLER__) || defined(__IAR_SYSTEMS_ASM__))
/** \brief GROUP register API structure */
typedef struct
{
  __IO  uint32_t                       PORT_DIR;           /**< Offset: 0x00 (R/W  32) Data Direction */
  __IO  uint32_t                       PORT_DIRCLR;        /**< Offset: 0x04 (R/W  32) Data Direction Clear */
  __IO  uint32_t                       PORT_DIRSET;        /**< Offset: 0x08 (R/W  32) Data Direction Set */
  __IO  uint32_t                       PORT_DIRTGL;        /**< Offset: 0x0C (R/W  32) Data Direction Toggle */
  __IO  uint32_t                       PORT_OUT;           /**< Offset: 0x10 (R/W  32) Data Output Value */
  __IO  uint32_t                       PORT_OUTCLR;        /**< Offset: 0x14 (R/W  32) Data Output Value Clear */
  __IO  uint32_t                       PORT_OUTSET;        /**< Offset: 0x18 (R/W  32) Data Output Value Set */
  __IO  uint32_t                       PORT_OUTTGL;        /**< Offset: 0x1C (R/W  32) Data Output Value Toggle */
  __I   uint32_t                       PORT_IN;            /**< Offset: 0x20 (R/   32) Data Input Value */
  __IO  uint32_t                       PORT_CTRL;          /**< Offset: 0x24 (R/W  32) Control */
  __O   uint32_t                       PORT_WRCONFIG;      /**< Offset: 0x28 ( /W  32) Write Configuration */
  __IO  uint32_t                       PORT_EVCTRL;        /**< Offset: 0x2C (R/W  32) Event Input Control */
  __IO  uint8_t                        PORT_PMUX[16];      /**< Offset: 0x30 (R/W  8) Peripheral Multiplexing */
  __IO  uint8_t                        PORT_PINCFG[32];    /**< Offset: 0x40 (R/W  8) Pin Configuration */
  __I   uint8_t                        Reserved1[0x20];
} port_group_registers_t;

#define PORT_GROUP_NUMBER 3

/** \brief PORT register API structure */
typedef struct
{  /* Port Module */
        port_group_registers_t         GROUP[PORT_GROUP_NUMBER]; /**< Offset: 0x00  */
} port_registers_t;


#endif /* !(defined(__ASSEMBLER__) || defined(__IAR_SYSTEMS_ASM__)) */
#endif /* _PIC32CMLE00_PORT_COMPONENT_H_ */
