ice458/RPN_Scientific_Calc/src/packs/PIC32CM2532LE00048_DFP/component/ac.h

/*
 * Component description for AC
 *
 * Copyright (c) 2023 Microchip Technology Inc. and its subsidiaries.
 *
 * Subject to your compliance with these terms, you may use Microchip software and any derivatives
 * exclusively with Microchip products. It is your responsibility to comply with third party license
 * terms applicable to your use of third party software (including open source software) that may
 * accompany Microchip software.
 *
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
 * IN NO EVENT WILL MICROCHIP BE LIABLE FOR ANY INDIRECT, SPECIAL, PUNITIVE, INCIDENTAL OR CONSEQUENTIAL
 * LOSS, DAMAGE, COST OR EXPENSE OF ANY KIND WHATSOEVER RELATED TO THE SOFTWARE, HOWEVER CAUSED, EVEN IF
 * MICROCHIP HAS BEEN ADVISED OF THE POSSIBILITY OR THE DAMAGES ARE FORESEEABLE. TO THE FULLEST EXTENT
 * ALLOWED BY LAW, MICROCHIP'S TOTAL LIABILITY ON ALL CLAIMS IN ANY WAY RELATED TO THIS SOFTWARE WILL NOT
 * EXCEED THE AMOUNT OF FEES, IF ANY, THAT YOU HAVE PAID DIRECTLY TO MICROCHIP FOR THIS SOFTWARE.
 *
 */

/* file generated from device description version 2022-09-09T06:08:26Z */
#ifndef _PIC32CMLE00_AC_COMPONENT_H_
#define _PIC32CMLE00_AC_COMPONENT_H_

/* ************************************************************************** */
/*   SOFTWARE API DEFINITION FOR AC                                           */
/* ************************************************************************** */

/* -------- AC_CTRLA : (AC Offset: 0x00) (R/W 8) Control A -------- */
#define AC_CTRLA_RESETVALUE                   _UINT8_(0x00)                                        /*  (AC_CTRLA) Control A  Reset Value */

#define AC_CTRLA_SWRST_Pos                    _UINT8_(0)                                           /* (AC_CTRLA) Software Reset Position */
#define AC_CTRLA_SWRST_Msk                    (_UINT8_(0x1) << AC_CTRLA_SWRST_Pos)                 /* (AC_CTRLA) Software Reset Mask */
#define AC_CTRLA_SWRST(value)                 (AC_CTRLA_SWRST_Msk & (_UINT8_(value) << AC_CTRLA_SWRST_Pos)) /* Assigment of value for SWRST in the AC_CTRLA register */
#define AC_CTRLA_ENABLE_Pos                   _UINT8_(1)                                           /* (AC_CTRLA) Enable Position */
#define AC_CTRLA_ENABLE_Msk                   (_UINT8_(0x1) << AC_CTRLA_ENABLE_Pos)                /* (AC_CTRLA) Enable Mask */
#define AC_CTRLA_ENABLE(value)                (AC_CTRLA_ENABLE_Msk & (_UINT8_(value) << AC_CTRLA_ENABLE_Pos)) /* Assigment of value for ENABLE in the AC_CTRLA register */
#define AC_CTRLA_Msk                          _UINT8_(0x03)                                        /* (AC_CTRLA) Register Mask  */


/* -------- AC_CTRLB : (AC Offset: 0x01) (R/W 8) Control B -------- */
#define AC_CTRLB_RESETVALUE                   _UINT8_(0x00)                                        /*  (AC_CTRLB) Control B  Reset Value */

#define AC_CTRLB_START0_Pos                   _UINT8_(0)                                           /* (AC_CTRLB) Comparator 0 Start Comparison Position */
#define AC_CTRLB_START0_Msk                   (_UINT8_(0x1) << AC_CTRLB_START0_Pos)                /* (AC_CTRLB) Comparator 0 Start Comparison Mask */
#define AC_CTRLB_START0(value)                (AC_CTRLB_START0_Msk & (_UINT8_(value) << AC_CTRLB_START0_Pos)) /* Assigment of value for START0 in the AC_CTRLB register */
#define AC_CTRLB_START1_Pos                   _UINT8_(1)                                           /* (AC_CTRLB) Comparator 1 Start Comparison Position */
#define AC_CTRLB_START1_Msk                   (_UINT8_(0x1) << AC_CTRLB_START1_Pos)                /* (AC_CTRLB) Comparator 1 Start Comparison Mask */
#define AC_CTRLB_START1(value)                (AC_CTRLB_START1_Msk & (_UINT8_(value) << AC_CTRLB_START1_Pos)) /* Assigment of value for START1 in the AC_CTRLB register */
#define AC_CTRLB_START2_Pos                   _UINT8_(2)                                           /* (AC_CTRLB) Comparator 2 Start Comparison Position */
#define AC_CTRLB_START2_Msk                   (_UINT8_(0x1) << AC_CTRLB_START2_Pos)                /* (AC_CTRLB) Comparator 2 Start Comparison Mask */
#define AC_CTRLB_START2(value)                (AC_CTRLB_START2_Msk & (_UINT8_(value) << AC_CTRLB_START2_Pos)) /* Assigment of value for START2 in the AC_CTRLB register */
#define AC_CTRLB_START3_Pos                   _UINT8_(3)                                           /* (AC_CTRLB) Comparator 3 Start Comparison Position */
#define AC_CTRLB_START3_Msk                   (_UINT8_(0x1) << AC_CTRLB_START3_Pos)                /* (AC_CTRLB) Comparator 3 Start Comparison Mask */
#define AC_CTRLB_START3(value)                (AC_CTRLB_START3_Msk & (_UINT8_(value) << AC_CTRLB_START3_Pos)) /* Assigment of value for START3 in the AC_CTRLB register */
#define AC_CTRLB_Msk                          _UINT8_(0x0F)                                        /* (AC_CTRLB) Register Mask  */

#define AC_CTRLB_START_Pos                    _UINT8_(0)                                           /* (AC_CTRLB Position) Comparator 3 Start Comparison */
#define AC_CTRLB_START_Msk                    (_UINT8_(0xF) << AC_CTRLB_START_Pos)                 /* (AC_CTRLB Mask) START */
#define AC_CTRLB_START(value)                 (AC_CTRLB_START_Msk & (_UINT8_(value) << AC_CTRLB_START_Pos)) 

/* -------- AC_EVCTRL : (AC Offset: 0x02) (R/W 16) Event Control -------- */
#define AC_EVCTRL_RESETVALUE                  _UINT16_(0x00)                                       /*  (AC_EVCTRL) Event Control  Reset Value */

#define AC_EVCTRL_COMPEO0_Pos                 _UINT16_(0)                                          /* (AC_EVCTRL) Comparator 0 Event Output Enable Position */
#define AC_EVCTRL_COMPEO0_Msk                 (_UINT16_(0x1) << AC_EVCTRL_COMPEO0_Pos)             /* (AC_EVCTRL) Comparator 0 Event Output Enable Mask */
#define AC_EVCTRL_COMPEO0(value)              (AC_EVCTRL_COMPEO0_Msk & (_UINT16_(value) << AC_EVCTRL_COMPEO0_Pos)) /* Assigment of value for COMPEO0 in the AC_EVCTRL register */
#define AC_EVCTRL_COMPEO1_Pos                 _UINT16_(1)                                          /* (AC_EVCTRL) Comparator 1 Event Output Enable Position */
#define AC_EVCTRL_COMPEO1_Msk                 (_UINT16_(0x1) << AC_EVCTRL_COMPEO1_Pos)             /* (AC_EVCTRL) Comparator 1 Event Output Enable Mask */
#define AC_EVCTRL_COMPEO1(value)              (AC_EVCTRL_COMPEO1_Msk & (_UINT16_(value) << AC_EVCTRL_COMPEO1_Pos)) /* Assigment of value for COMPEO1 in the AC_EVCTRL register */
#define AC_EVCTRL_COMPEO2_Pos                 _UINT16_(2)                                          /* (AC_EVCTRL) Comparator 2 Event Output Enable Position */
#define AC_EVCTRL_COMPEO2_Msk                 (_UINT16_(0x1) << AC_EVCTRL_COMPEO2_Pos)             /* (AC_EVCTRL) Comparator 2 Event Output Enable Mask */
#define AC_EVCTRL_COMPEO2(value)              (AC_EVCTRL_COMPEO2_Msk & (_UINT16_(value) << AC_EVCTRL_COMPEO2_Pos)) /* Assigment of value for COMPEO2 in the AC_EVCTRL register */
#define AC_EVCTRL_COMPEO3_Pos                 _UINT16_(3)                                          /* (AC_EVCTRL) Comparator 3 Event Output Enable Position */
#define AC_EVCTRL_COMPEO3_Msk                 (_UINT16_(0x1) << AC_EVCTRL_COMPEO3_Pos)             /* (AC_EVCTRL) Comparator 3 Event Output Enable Mask */
#define AC_EVCTRL_COMPEO3(value)              (AC_EVCTRL_COMPEO3_Msk & (_UINT16_(value) << AC_EVCTRL_COMPEO3_Pos)) /* Assigment of value for COMPEO3 in the AC_EVCTRL register */
#define AC_EVCTRL_WINEO0_Pos                  _UINT16_(4)                                          /* (AC_EVCTRL) Window 0 Event Output Enable Position */
#define AC_EVCTRL_WINEO0_Msk                  (_UINT16_(0x1) << AC_EVCTRL_WINEO0_Pos)              /* (AC_EVCTRL) Window 0 Event Output Enable Mask */
#define AC_EVCTRL_WINEO0(value)               (AC_EVCTRL_WINEO0_Msk & (_UINT16_(value) << AC_EVCTRL_WINEO0_Pos)) /* Assigment of value for WINEO0 in the AC_EVCTRL register */
#define AC_EVCTRL_WINEO1_Pos                  _UINT16_(5)                                          /* (AC_EVCTRL) Window 1 Event Output Enable Position */
#define AC_EVCTRL_WINEO1_Msk                  (_UINT16_(0x1) << AC_EVCTRL_WINEO1_Pos)              /* (AC_EVCTRL) Window 1 Event Output Enable Mask */
#define AC_EVCTRL_WINEO1(value)               (AC_EVCTRL_WINEO1_Msk & (_UINT16_(value) << AC_EVCTRL_WINEO1_Pos)) /* Assigment of value for WINEO1 in the AC_EVCTRL register */
#define AC_EVCTRL_COMPEI0_Pos                 _UINT16_(8)                                          /* (AC_EVCTRL) Comparator 0 Event Input Enable Position */
#define AC_EVCTRL_COMPEI0_Msk                 (_UINT16_(0x1) << AC_EVCTRL_COMPEI0_Pos)             /* (AC_EVCTRL) Comparator 0 Event Input Enable Mask */
#define AC_EVCTRL_COMPEI0(value)              (AC_EVCTRL_COMPEI0_Msk & (_UINT16_(value) << AC_EVCTRL_COMPEI0_Pos)) /* Assigment of value for COMPEI0 in the AC_EVCTRL register */
#define AC_EVCTRL_COMPEI1_Pos                 _UINT16_(9)                                          /* (AC_EVCTRL) Comparator 1 Event Input Enable Position */
#define AC_EVCTRL_COMPEI1_Msk                 (_UINT16_(0x1) << AC_EVCTRL_COMPEI1_Pos)             /* (AC_EVCTRL) Comparator 1 Event Input Enable Mask */
#define AC_EVCTRL_COMPEI1(value)              (AC_EVCTRL_COMPEI1_Msk & (_UINT16_(value) << AC_EVCTRL_COMPEI1_Pos)) /* Assigment of value for COMPEI1 in the AC_EVCTRL register */
#define AC_EVCTRL_COMPEI2_Pos                 _UINT16_(10)                                         /* (AC_EVCTRL) Comparator 2 Event Input Enable Position */
#define AC_EVCTRL_COMPEI2_Msk                 (_UINT16_(0x1) << AC_EVCTRL_COMPEI2_Pos)             /* (AC_EVCTRL) Comparator 2 Event Input Enable Mask */
#define AC_EVCTRL_COMPEI2(value)              (AC_EVCTRL_COMPEI2_Msk & (_UINT16_(value) << AC_EVCTRL_COMPEI2_Pos)) /* Assigment of value for COMPEI2 in the AC_EVCTRL register */
#define AC_EVCTRL_COMPEI3_Pos                 _UINT16_(11)                                         /* (AC_EVCTRL) Comparator 3 Event Input Enable Position */
#define AC_EVCTRL_COMPEI3_Msk                 (_UINT16_(0x1) << AC_EVCTRL_COMPEI3_Pos)             /* (AC_EVCTRL) Comparator 3 Event Input Enable Mask */
#define AC_EVCTRL_COMPEI3(value)              (AC_EVCTRL_COMPEI3_Msk & (_UINT16_(value) << AC_EVCTRL_COMPEI3_Pos)) /* Assigment of value for COMPEI3 in the AC_EVCTRL register */
#define AC_EVCTRL_INVEI0_Pos                  _UINT16_(12)                                         /* (AC_EVCTRL) Comparator 0 Input Event Invert Enable Position */
#define AC_EVCTRL_INVEI0_Msk                  (_UINT16_(0x1) << AC_EVCTRL_INVEI0_Pos)              /* (AC_EVCTRL) Comparator 0 Input Event Invert Enable Mask */
#define AC_EVCTRL_INVEI0(value)               (AC_EVCTRL_INVEI0_Msk & (_UINT16_(value) << AC_EVCTRL_INVEI0_Pos)) /* Assigment of value for INVEI0 in the AC_EVCTRL register */
#define AC_EVCTRL_INVEI1_Pos                  _UINT16_(13)                                         /* (AC_EVCTRL) Comparator 1 Input Event Invert Enable Position */
#define AC_EVCTRL_INVEI1_Msk                  (_UINT16_(0x1) << AC_EVCTRL_INVEI1_Pos)              /* (AC_EVCTRL) Comparator 1 Input Event Invert Enable Mask */
#define AC_EVCTRL_INVEI1(value)               (AC_EVCTRL_INVEI1_Msk & (_UINT16_(value) << AC_EVCTRL_INVEI1_Pos)) /* Assigment of value for INVEI1 in the AC_EVCTRL register */
#define AC_EVCTRL_INVEI2_Pos                  _UINT16_(14)                                         /* (AC_EVCTRL) Comparator 2 Input Event Invert Enable Position */
#define AC_EVCTRL_INVEI2_Msk                  (_UINT16_(0x1) << AC_EVCTRL_INVEI2_Pos)              /* (AC_EVCTRL) Comparator 2 Input Event Invert Enable Mask */
#define AC_EVCTRL_INVEI2(value)               (AC_EVCTRL_INVEI2_Msk & (_UINT16_(value) << AC_EVCTRL_INVEI2_Pos)) /* Assigment of value for INVEI2 in the AC_EVCTRL register */
#define AC_EVCTRL_INVEI3_Pos                  _UINT16_(15)                                         /* (AC_EVCTRL) Comparator 3 Input Event Invert Enable Position */
#define AC_EVCTRL_INVEI3_Msk                  (_UINT16_(0x1) << AC_EVCTRL_INVEI3_Pos)              /* (AC_EVCTRL) Comparator 3 Input Event Invert Enable Mask */
#define AC_EVCTRL_INVEI3(value)               (AC_EVCTRL_INVEI3_Msk & (_UINT16_(value) << AC_EVCTRL_INVEI3_Pos)) /* Assigment of value for INVEI3 in the AC_EVCTRL register */
#define AC_EVCTRL_Msk                         _UINT16_(0xFF3F)                                     /* (AC_EVCTRL) Register Mask  */

#define AC_EVCTRL_COMPEO_Pos                  _UINT16_(0)                                          /* (AC_EVCTRL Position) Comparator x Event Output Enable */
#define AC_EVCTRL_COMPEO_Msk                  (_UINT16_(0xF) << AC_EVCTRL_COMPEO_Pos)              /* (AC_EVCTRL Mask) COMPEO */
#define AC_EVCTRL_COMPEO(value)               (AC_EVCTRL_COMPEO_Msk & (_UINT16_(value) << AC_EVCTRL_COMPEO_Pos)) 
#define AC_EVCTRL_WINEO_Pos                   _UINT16_(4)                                          /* (AC_EVCTRL Position) Window x Event Output Enable */
#define AC_EVCTRL_WINEO_Msk                   (_UINT16_(0x3) << AC_EVCTRL_WINEO_Pos)               /* (AC_EVCTRL Mask) WINEO */
#define AC_EVCTRL_WINEO(value)                (AC_EVCTRL_WINEO_Msk & (_UINT16_(value) << AC_EVCTRL_WINEO_Pos)) 
#define AC_EVCTRL_COMPEI_Pos                  _UINT16_(8)                                          /* (AC_EVCTRL Position) Comparator x Event Input Enable */
#define AC_EVCTRL_COMPEI_Msk                  (_UINT16_(0xF) << AC_EVCTRL_COMPEI_Pos)              /* (AC_EVCTRL Mask) COMPEI */
#define AC_EVCTRL_COMPEI(value)               (AC_EVCTRL_COMPEI_Msk & (_UINT16_(value) << AC_EVCTRL_COMPEI_Pos)) 
#define AC_EVCTRL_INVEI_Pos                   _UINT16_(12)                                         /* (AC_EVCTRL Position) Comparator 3 Input Event Invert Enable */
#define AC_EVCTRL_INVEI_Msk                   (_UINT16_(0xF) << AC_EVCTRL_INVEI_Pos)               /* (AC_EVCTRL Mask) INVEI */
#define AC_EVCTRL_INVEI(value)                (AC_EVCTRL_INVEI_Msk & (_UINT16_(value) << AC_EVCTRL_INVEI_Pos)) 

/* -------- AC_INTENCLR : (AC Offset: 0x04) (R/W 8) Interrupt Enable Clear -------- */
#define AC_INTENCLR_RESETVALUE                _UINT8_(0x00)                                        /*  (AC_INTENCLR) Interrupt Enable Clear  Reset Value */

#define AC_INTENCLR_COMP0_Pos                 _UINT8_(0)                                           /* (AC_INTENCLR) Comparator 0 Interrupt Enable Position */
#define AC_INTENCLR_COMP0_Msk                 (_UINT8_(0x1) << AC_INTENCLR_COMP0_Pos)              /* (AC_INTENCLR) Comparator 0 Interrupt Enable Mask */
#define AC_INTENCLR_COMP0(value)              (AC_INTENCLR_COMP0_Msk & (_UINT8_(value) << AC_INTENCLR_COMP0_Pos)) /* Assigment of value for COMP0 in the AC_INTENCLR register */
#define AC_INTENCLR_COMP1_Pos                 _UINT8_(1)                                           /* (AC_INTENCLR) Comparator 1 Interrupt Enable Position */
#define AC_INTENCLR_COMP1_Msk                 (_UINT8_(0x1) << AC_INTENCLR_COMP1_Pos)              /* (AC_INTENCLR) Comparator 1 Interrupt Enable Mask */
#define AC_INTENCLR_COMP1(value)              (AC_INTENCLR_COMP1_Msk & (_UINT8_(value) << AC_INTENCLR_COMP1_Pos)) /* Assigment of value for COMP1 in the AC_INTENCLR register */
#define AC_INTENCLR_COMP2_Pos                 _UINT8_(2)                                           /* (AC_INTENCLR) Comparator 2 Interrupt Enable Position */
#define AC_INTENCLR_COMP2_Msk                 (_UINT8_(0x1) << AC_INTENCLR_COMP2_Pos)              /* (AC_INTENCLR) Comparator 2 Interrupt Enable Mask */
#define AC_INTENCLR_COMP2(value)              (AC_INTENCLR_COMP2_Msk & (_UINT8_(value) << AC_INTENCLR_COMP2_Pos)) /* Assigment of value for COMP2 in the AC_INTENCLR register */
#define AC_INTENCLR_COMP3_Pos                 _UINT8_(3)                                           /* (AC_INTENCLR) Comparator 3 Interrupt Enable Position */
#define AC_INTENCLR_COMP3_Msk                 (_UINT8_(0x1) << AC_INTENCLR_COMP3_Pos)              /* (AC_INTENCLR) Comparator 3 Interrupt Enable Mask */
#define AC_INTENCLR_COMP3(value)              (AC_INTENCLR_COMP3_Msk & (_UINT8_(value) << AC_INTENCLR_COMP3_Pos)) /* Assigment of value for COMP3 in the AC_INTENCLR register */
#define AC_INTENCLR_WIN0_Pos                  _UINT8_(4)                                           /* (AC_INTENCLR) Window 0 Interrupt Enable Position */
#define AC_INTENCLR_WIN0_Msk                  (_UINT8_(0x1) << AC_INTENCLR_WIN0_Pos)               /* (AC_INTENCLR) Window 0 Interrupt Enable Mask */
#define AC_INTENCLR_WIN0(value)               (AC_INTENCLR_WIN0_Msk & (_UINT8_(value) << AC_INTENCLR_WIN0_Pos)) /* Assigment of value for WIN0 in the AC_INTENCLR register */
#define AC_INTENCLR_WIN1_Pos                  _UINT8_(5)                                           /* (AC_INTENCLR) Window 1 Interrupt Enable Position */
#define AC_INTENCLR_WIN1_Msk                  (_UINT8_(0x1) << AC_INTENCLR_WIN1_Pos)               /* (AC_INTENCLR) Window 1 Interrupt Enable Mask */
#define AC_INTENCLR_WIN1(value)               (AC_INTENCLR_WIN1_Msk & (_UINT8_(value) << AC_INTENCLR_WIN1_Pos)) /* Assigment of value for WIN1 in the AC_INTENCLR register */
#define AC_INTENCLR_Msk                       _UINT8_(0x3F)                                        /* (AC_INTENCLR) Register Mask  */

#define AC_INTENCLR_COMP_Pos                  _UINT8_(0)                                           /* (AC_INTENCLR Position) Comparator x Interrupt Enable */
#define AC_INTENCLR_COMP_Msk                  (_UINT8_(0xF) << AC_INTENCLR_COMP_Pos)               /* (AC_INTENCLR Mask) COMP */
#define AC_INTENCLR_COMP(value)               (AC_INTENCLR_COMP_Msk & (_UINT8_(value) << AC_INTENCLR_COMP_Pos)) 
#define AC_INTENCLR_WIN_Pos                   _UINT8_(4)                                           /* (AC_INTENCLR Position) Window x Interrupt Enable */
#define AC_INTENCLR_WIN_Msk                   (_UINT8_(0x3) << AC_INTENCLR_WIN_Pos)                /* (AC_INTENCLR Mask) WIN */
#define AC_INTENCLR_WIN(value)                (AC_INTENCLR_WIN_Msk & (_UINT8_(value) << AC_INTENCLR_WIN_Pos)) 

/* -------- AC_INTENSET : (AC Offset: 0x05) (R/W 8) Interrupt Enable Set -------- */
#define AC_INTENSET_RESETVALUE                _UINT8_(0x00)                                        /*  (AC_INTENSET) Interrupt Enable Set  Reset Value */

#define AC_INTENSET_COMP0_Pos                 _UINT8_(0)                                           /* (AC_INTENSET) Comparator 0 Interrupt Enable Position */
#define AC_INTENSET_COMP0_Msk                 (_UINT8_(0x1) << AC_INTENSET_COMP0_Pos)              /* (AC_INTENSET) Comparator 0 Interrupt Enable Mask */
#define AC_INTENSET_COMP0(value)              (AC_INTENSET_COMP0_Msk & (_UINT8_(value) << AC_INTENSET_COMP0_Pos)) /* Assigment of value for COMP0 in the AC_INTENSET register */
#define AC_INTENSET_COMP1_Pos                 _UINT8_(1)                                           /* (AC_INTENSET) Comparator 1 Interrupt Enable Position */
#define AC_INTENSET_COMP1_Msk                 (_UINT8_(0x1) << AC_INTENSET_COMP1_Pos)              /* (AC_INTENSET) Comparator 1 Interrupt Enable Mask */
#define AC_INTENSET_COMP1(value)              (AC_INTENSET_COMP1_Msk & (_UINT8_(value) << AC_INTENSET_COMP1_Pos)) /* Assigment of value for COMP1 in the AC_INTENSET register */
#define AC_INTENSET_COMP2_Pos                 _UINT8_(2)                                           /* (AC_INTENSET) Comparator 2 Interrupt Enable Position */
#define AC_INTENSET_COMP2_Msk                 (_UINT8_(0x1) << AC_INTENSET_COMP2_Pos)              /* (AC_INTENSET) Comparator 2 Interrupt Enable Mask */
#define AC_INTENSET_COMP2(value)              (AC_INTENSET_COMP2_Msk & (_UINT8_(value) << AC_INTENSET_COMP2_Pos)) /* Assigment of value for COMP2 in the AC_INTENSET register */
#define AC_INTENSET_COMP3_Pos                 _UINT8_(3)                                           /* (AC_INTENSET) Comparator 3 Interrupt Enable Position */
#define AC_INTENSET_COMP3_Msk                 (_UINT8_(0x1) << AC_INTENSET_COMP3_Pos)              /* (AC_INTENSET) Comparator 3 Interrupt Enable Mask */
#define AC_INTENSET_COMP3(value)              (AC_INTENSET_COMP3_Msk & (_UINT8_(value) << AC_INTENSET_COMP3_Pos)) /* Assigment of value for COMP3 in the AC_INTENSET register */
#define AC_INTENSET_WIN0_Pos                  _UINT8_(4)                                           /* (AC_INTENSET) Window 0 Interrupt Enable Position */
#define AC_INTENSET_WIN0_Msk                  (_UINT8_(0x1) << AC_INTENSET_WIN0_Pos)               /* (AC_INTENSET) Window 0 Interrupt Enable Mask */
#define AC_INTENSET_WIN0(value)               (AC_INTENSET_WIN0_Msk & (_UINT8_(value) << AC_INTENSET_WIN0_Pos)) /* Assigment of value for WIN0 in the AC_INTENSET register */
#define AC_INTENSET_WIN1_Pos                  _UINT8_(5)                                           /* (AC_INTENSET) Window 1 Interrupt Enable Position */
#define AC_INTENSET_WIN1_Msk                  (_UINT8_(0x1) << AC_INTENSET_WIN1_Pos)               /* (AC_INTENSET) Window 1 Interrupt Enable Mask */
#define AC_INTENSET_WIN1(value)               (AC_INTENSET_WIN1_Msk & (_UINT8_(value) << AC_INTENSET_WIN1_Pos)) /* Assigment of value for WIN1 in the AC_INTENSET register */
#define AC_INTENSET_Msk                       _UINT8_(0x3F)                                        /* (AC_INTENSET) Register Mask  */

#define AC_INTENSET_COMP_Pos                  _UINT8_(0)                                           /* (AC_INTENSET Position) Comparator x Interrupt Enable */
#define AC_INTENSET_COMP_Msk                  (_UINT8_(0xF) << AC_INTENSET_COMP_Pos)               /* (AC_INTENSET Mask) COMP */
#define AC_INTENSET_COMP(value)               (AC_INTENSET_COMP_Msk & (_UINT8_(value) << AC_INTENSET_COMP_Pos)) 
#define AC_INTENSET_WIN_Pos                   _UINT8_(4)                                           /* (AC_INTENSET Position) Window x Interrupt Enable */
#define AC_INTENSET_WIN_Msk                   (_UINT8_(0x3) << AC_INTENSET_WIN_Pos)                /* (AC_INTENSET Mask) WIN */
#define AC_INTENSET_WIN(value)                (AC_INTENSET_WIN_Msk & (_UINT8_(value) << AC_INTENSET_WIN_Pos)) 

/* -------- AC_INTFLAG : (AC Offset: 0x06) (R/W 8) Interrupt Flag Status and Clear -------- */
#define AC_INTFLAG_RESETVALUE                 _UINT8_(0x00)                                        /*  (AC_INTFLAG) Interrupt Flag Status and Clear  Reset Value */

#define AC_INTFLAG_COMP0_Pos                  _UINT8_(0)                                           /* (AC_INTFLAG) Comparator 0 Position */
#define AC_INTFLAG_COMP0_Msk                  (_UINT8_(0x1) << AC_INTFLAG_COMP0_Pos)               /* (AC_INTFLAG) Comparator 0 Mask */
#define AC_INTFLAG_COMP0(value)               (AC_INTFLAG_COMP0_Msk & (_UINT8_(value) << AC_INTFLAG_COMP0_Pos)) /* Assigment of value for COMP0 in the AC_INTFLAG register */
#define AC_INTFLAG_COMP1_Pos                  _UINT8_(1)                                           /* (AC_INTFLAG) Comparator 1 Position */
#define AC_INTFLAG_COMP1_Msk                  (_UINT8_(0x1) << AC_INTFLAG_COMP1_Pos)               /* (AC_INTFLAG) Comparator 1 Mask */
#define AC_INTFLAG_COMP1(value)               (AC_INTFLAG_COMP1_Msk & (_UINT8_(value) << AC_INTFLAG_COMP1_Pos)) /* Assigment of value for COMP1 in the AC_INTFLAG register */
#define AC_INTFLAG_COMP2_Pos                  _UINT8_(2)                                           /* (AC_INTFLAG) Comparator 2 Position */
#define AC_INTFLAG_COMP2_Msk                  (_UINT8_(0x1) << AC_INTFLAG_COMP2_Pos)               /* (AC_INTFLAG) Comparator 2 Mask */
#define AC_INTFLAG_COMP2(value)               (AC_INTFLAG_COMP2_Msk & (_UINT8_(value) << AC_INTFLAG_COMP2_Pos)) /* Assigment of value for COMP2 in the AC_INTFLAG register */
#define AC_INTFLAG_COMP3_Pos                  _UINT8_(3)                                           /* (AC_INTFLAG) Comparator 3 Position */
#define AC_INTFLAG_COMP3_Msk                  (_UINT8_(0x1) << AC_INTFLAG_COMP3_Pos)               /* (AC_INTFLAG) Comparator 3 Mask */
#define AC_INTFLAG_COMP3(value)               (AC_INTFLAG_COMP3_Msk & (_UINT8_(value) << AC_INTFLAG_COMP3_Pos)) /* Assigment of value for COMP3 in the AC_INTFLAG register */
#define AC_INTFLAG_WIN0_Pos                   _UINT8_(4)                                           /* (AC_INTFLAG) Window 0 Position */
#define AC_INTFLAG_WIN0_Msk                   (_UINT8_(0x1) << AC_INTFLAG_WIN0_Pos)                /* (AC_INTFLAG) Window 0 Mask */
#define AC_INTFLAG_WIN0(value)                (AC_INTFLAG_WIN0_Msk & (_UINT8_(value) << AC_INTFLAG_WIN0_Pos)) /* Assigment of value for WIN0 in the AC_INTFLAG register */
#define AC_INTFLAG_WIN1_Pos                   _UINT8_(5)                                           /* (AC_INTFLAG) Window 1 Position */
#define AC_INTFLAG_WIN1_Msk                   (_UINT8_(0x1) << AC_INTFLAG_WIN1_Pos)                /* (AC_INTFLAG) Window 1 Mask */
#define AC_INTFLAG_WIN1(value)                (AC_INTFLAG_WIN1_Msk & (_UINT8_(value) << AC_INTFLAG_WIN1_Pos)) /* Assigment of value for WIN1 in the AC_INTFLAG register */
#define AC_INTFLAG_Msk                        _UINT8_(0x3F)                                        /* (AC_INTFLAG) Register Mask  */

#define AC_INTFLAG_COMP_Pos                   _UINT8_(0)                                           /* (AC_INTFLAG Position) Comparator x */
#define AC_INTFLAG_COMP_Msk                   (_UINT8_(0xF) << AC_INTFLAG_COMP_Pos)                /* (AC_INTFLAG Mask) COMP */
#define AC_INTFLAG_COMP(value)                (AC_INTFLAG_COMP_Msk & (_UINT8_(value) << AC_INTFLAG_COMP_Pos)) 
#define AC_INTFLAG_WIN_Pos                    _UINT8_(4)                                           /* (AC_INTFLAG Position) Window x */
#define AC_INTFLAG_WIN_Msk                    (_UINT8_(0x3) << AC_INTFLAG_WIN_Pos)                 /* (AC_INTFLAG Mask) WIN */
#define AC_INTFLAG_WIN(value)                 (AC_INTFLAG_WIN_Msk & (_UINT8_(value) << AC_INTFLAG_WIN_Pos)) 

/* -------- AC_STATUSA : (AC Offset: 0x07) ( R/ 8) Status A -------- */
#define AC_STATUSA_RESETVALUE                 _UINT8_(0x00)                                        /*  (AC_STATUSA) Status A  Reset Value */

#define AC_STATUSA_STATE0_Pos                 _UINT8_(0)                                           /* (AC_STATUSA) Comparator 0 Current State Position */
#define AC_STATUSA_STATE0_Msk                 (_UINT8_(0x1) << AC_STATUSA_STATE0_Pos)              /* (AC_STATUSA) Comparator 0 Current State Mask */
#define AC_STATUSA_STATE0(value)              (AC_STATUSA_STATE0_Msk & (_UINT8_(value) << AC_STATUSA_STATE0_Pos)) /* Assigment of value for STATE0 in the AC_STATUSA register */
#define AC_STATUSA_STATE1_Pos                 _UINT8_(1)                                           /* (AC_STATUSA) Comparator 1 Current State Position */
#define AC_STATUSA_STATE1_Msk                 (_UINT8_(0x1) << AC_STATUSA_STATE1_Pos)              /* (AC_STATUSA) Comparator 1 Current State Mask */
#define AC_STATUSA_STATE1(value)              (AC_STATUSA_STATE1_Msk & (_UINT8_(value) << AC_STATUSA_STATE1_Pos)) /* Assigment of value for STATE1 in the AC_STATUSA register */
#define AC_STATUSA_STATE2_Pos                 _UINT8_(2)                                           /* (AC_STATUSA) Comparator 2 Current State Position */
#define AC_STATUSA_STATE2_Msk                 (_UINT8_(0x1) << AC_STATUSA_STATE2_Pos)              /* (AC_STATUSA) Comparator 2 Current State Mask */
#define AC_STATUSA_STATE2(value)              (AC_STATUSA_STATE2_Msk & (_UINT8_(value) << AC_STATUSA_STATE2_Pos)) /* Assigment of value for STATE2 in the AC_STATUSA register */
#define AC_STATUSA_STATE3_Pos                 _UINT8_(3)                                           /* (AC_STATUSA) Comparator 3 Current State Position */
#define AC_STATUSA_STATE3_Msk                 (_UINT8_(0x1) << AC_STATUSA_STATE3_Pos)              /* (AC_STATUSA) Comparator 3 Current State Mask */
#define AC_STATUSA_STATE3(value)              (AC_STATUSA_STATE3_Msk & (_UINT8_(value) << AC_STATUSA_STATE3_Pos)) /* Assigment of value for STATE3 in the AC_STATUSA register */
#define AC_STATUSA_WSTATE0_Pos                _UINT8_(4)                                           /* (AC_STATUSA) Window 0 Current State Position */
#define AC_STATUSA_WSTATE0_Msk                (_UINT8_(0x3) << AC_STATUSA_WSTATE0_Pos)             /* (AC_STATUSA) Window 0 Current State Mask */
#define AC_STATUSA_WSTATE0(value)             (AC_STATUSA_WSTATE0_Msk & (_UINT8_(value) << AC_STATUSA_WSTATE0_Pos)) /* Assigment of value for WSTATE0 in the AC_STATUSA register */
#define   AC_STATUSA_WSTATE0_ABOVE_Val        _UINT8_(0x0)                                         /* (AC_STATUSA) Signal is above window  */
#define   AC_STATUSA_WSTATE0_INSIDE_Val       _UINT8_(0x1)                                         /* (AC_STATUSA) Signal is inside window  */
#define   AC_STATUSA_WSTATE0_BELOW_Val        _UINT8_(0x2)                                         /* (AC_STATUSA) Signal is below window  */
#define AC_STATUSA_WSTATE0_ABOVE              (AC_STATUSA_WSTATE0_ABOVE_Val << AC_STATUSA_WSTATE0_Pos) /* (AC_STATUSA) Signal is above window Position  */
#define AC_STATUSA_WSTATE0_INSIDE             (AC_STATUSA_WSTATE0_INSIDE_Val << AC_STATUSA_WSTATE0_Pos) /* (AC_STATUSA) Signal is inside window Position  */
#define AC_STATUSA_WSTATE0_BELOW              (AC_STATUSA_WSTATE0_BELOW_Val << AC_STATUSA_WSTATE0_Pos) /* (AC_STATUSA) Signal is below window Position  */
#define AC_STATUSA_WSTATE1_Pos                _UINT8_(6)                                           /* (AC_STATUSA) Window 1 Current State Position */
#define AC_STATUSA_WSTATE1_Msk                (_UINT8_(0x3) << AC_STATUSA_WSTATE1_Pos)             /* (AC_STATUSA) Window 1 Current State Mask */
#define AC_STATUSA_WSTATE1(value)             (AC_STATUSA_WSTATE1_Msk & (_UINT8_(value) << AC_STATUSA_WSTATE1_Pos)) /* Assigment of value for WSTATE1 in the AC_STATUSA register */
#define   AC_STATUSA_WSTATE1_ABOVE_Val        _UINT8_(0x0)                                         /* (AC_STATUSA) Signal is above window  */
#define   AC_STATUSA_WSTATE1_INSIDE_Val       _UINT8_(0x1)                                         /* (AC_STATUSA) Signal is inside window  */
#define   AC_STATUSA_WSTATE1_BELOW_Val        _UINT8_(0x2)                                         /* (AC_STATUSA) Signal is below window  */
#define AC_STATUSA_WSTATE1_ABOVE              (AC_STATUSA_WSTATE1_ABOVE_Val << AC_STATUSA_WSTATE1_Pos) /* (AC_STATUSA) Signal is above window Position  */
#define AC_STATUSA_WSTATE1_INSIDE             (AC_STATUSA_WSTATE1_INSIDE_Val << AC_STATUSA_WSTATE1_Pos) /* (AC_STATUSA) Signal is inside window Position  */
#define AC_STATUSA_WSTATE1_BELOW              (AC_STATUSA_WSTATE1_BELOW_Val << AC_STATUSA_WSTATE1_Pos) /* (AC_STATUSA) Signal is below window Position  */
#define AC_STATUSA_Msk                        _UINT8_(0xFF)                                        /* (AC_STATUSA) Register Mask  */

#define AC_STATUSA_STATE_Pos                  _UINT8_(0)                                           /* (AC_STATUSA Position) Comparator x Current State */
#define AC_STATUSA_STATE_Msk                  (_UINT8_(0xF) << AC_STATUSA_STATE_Pos)               /* (AC_STATUSA Mask) STATE */
#define AC_STATUSA_STATE(value)               (AC_STATUSA_STATE_Msk & (_UINT8_(value) << AC_STATUSA_STATE_Pos)) 

/* -------- AC_STATUSB : (AC Offset: 0x08) ( R/ 8) Status B -------- */
#define AC_STATUSB_RESETVALUE                 _UINT8_(0x00)                                        /*  (AC_STATUSB) Status B  Reset Value */

#define AC_STATUSB_READY0_Pos                 _UINT8_(0)                                           /* (AC_STATUSB) Comparator 0 Ready Position */
#define AC_STATUSB_READY0_Msk                 (_UINT8_(0x1) << AC_STATUSB_READY0_Pos)              /* (AC_STATUSB) Comparator 0 Ready Mask */
#define AC_STATUSB_READY0(value)              (AC_STATUSB_READY0_Msk & (_UINT8_(value) << AC_STATUSB_READY0_Pos)) /* Assigment of value for READY0 in the AC_STATUSB register */
#define AC_STATUSB_READY1_Pos                 _UINT8_(1)                                           /* (AC_STATUSB) Comparator 1 Ready Position */
#define AC_STATUSB_READY1_Msk                 (_UINT8_(0x1) << AC_STATUSB_READY1_Pos)              /* (AC_STATUSB) Comparator 1 Ready Mask */
#define AC_STATUSB_READY1(value)              (AC_STATUSB_READY1_Msk & (_UINT8_(value) << AC_STATUSB_READY1_Pos)) /* Assigment of value for READY1 in the AC_STATUSB register */
#define AC_STATUSB_READY2_Pos                 _UINT8_(2)                                           /* (AC_STATUSB) Comparator 2 Ready Position */
#define AC_STATUSB_READY2_Msk                 (_UINT8_(0x1) << AC_STATUSB_READY2_Pos)              /* (AC_STATUSB) Comparator 2 Ready Mask */
#define AC_STATUSB_READY2(value)              (AC_STATUSB_READY2_Msk & (_UINT8_(value) << AC_STATUSB_READY2_Pos)) /* Assigment of value for READY2 in the AC_STATUSB register */
#define AC_STATUSB_READY3_Pos                 _UINT8_(3)                                           /* (AC_STATUSB) Comparator 3 Ready Position */
#define AC_STATUSB_READY3_Msk                 (_UINT8_(0x1) << AC_STATUSB_READY3_Pos)              /* (AC_STATUSB) Comparator 3 Ready Mask */
#define AC_STATUSB_READY3(value)              (AC_STATUSB_READY3_Msk & (_UINT8_(value) << AC_STATUSB_READY3_Pos)) /* Assigment of value for READY3 in the AC_STATUSB register */
#define AC_STATUSB_Msk                        _UINT8_(0x0F)                                        /* (AC_STATUSB) Register Mask  */

#define AC_STATUSB_READY_Pos                  _UINT8_(0)                                           /* (AC_STATUSB Position) Comparator 3 Ready */
#define AC_STATUSB_READY_Msk                  (_UINT8_(0xF) << AC_STATUSB_READY_Pos)               /* (AC_STATUSB Mask) READY */
#define AC_STATUSB_READY(value)               (AC_STATUSB_READY_Msk & (_UINT8_(value) << AC_STATUSB_READY_Pos)) 

/* -------- AC_DBGCTRL : (AC Offset: 0x09) (R/W 8) Debug Control -------- */
#define AC_DBGCTRL_RESETVALUE                 _UINT8_(0x00)                                        /*  (AC_DBGCTRL) Debug Control  Reset Value */

#define AC_DBGCTRL_DBGRUN_Pos                 _UINT8_(0)                                           /* (AC_DBGCTRL) Debug Run Position */
#define AC_DBGCTRL_DBGRUN_Msk                 (_UINT8_(0x1) << AC_DBGCTRL_DBGRUN_Pos)              /* (AC_DBGCTRL) Debug Run Mask */
#define AC_DBGCTRL_DBGRUN(value)              (AC_DBGCTRL_DBGRUN_Msk & (_UINT8_(value) << AC_DBGCTRL_DBGRUN_Pos)) /* Assigment of value for DBGRUN in the AC_DBGCTRL register */
#define AC_DBGCTRL_Msk                        _UINT8_(0x01)                                        /* (AC_DBGCTRL) Register Mask  */


/* -------- AC_WINCTRL : (AC Offset: 0x0A) (R/W 8) Window Control -------- */
#define AC_WINCTRL_RESETVALUE                 _UINT8_(0x00)                                        /*  (AC_WINCTRL) Window Control  Reset Value */

#define AC_WINCTRL_WEN0_Pos                   _UINT8_(0)                                           /* (AC_WINCTRL) Window 0 Mode Enable Position */
#define AC_WINCTRL_WEN0_Msk                   (_UINT8_(0x1) << AC_WINCTRL_WEN0_Pos)                /* (AC_WINCTRL) Window 0 Mode Enable Mask */
#define AC_WINCTRL_WEN0(value)                (AC_WINCTRL_WEN0_Msk & (_UINT8_(value) << AC_WINCTRL_WEN0_Pos)) /* Assigment of value for WEN0 in the AC_WINCTRL register */
#define AC_WINCTRL_WINTSEL0_Pos               _UINT8_(1)                                           /* (AC_WINCTRL) Window 0 Interrupt Selection Position */
#define AC_WINCTRL_WINTSEL0_Msk               (_UINT8_(0x3) << AC_WINCTRL_WINTSEL0_Pos)            /* (AC_WINCTRL) Window 0 Interrupt Selection Mask */
#define AC_WINCTRL_WINTSEL0(value)            (AC_WINCTRL_WINTSEL0_Msk & (_UINT8_(value) << AC_WINCTRL_WINTSEL0_Pos)) /* Assigment of value for WINTSEL0 in the AC_WINCTRL register */
#define   AC_WINCTRL_WINTSEL0_ABOVE_Val       _UINT8_(0x0)                                         /* (AC_WINCTRL) Interrupt on signal above window  */
#define   AC_WINCTRL_WINTSEL0_INSIDE_Val      _UINT8_(0x1)                                         /* (AC_WINCTRL) Interrupt on signal inside window  */
#define   AC_WINCTRL_WINTSEL0_BELOW_Val       _UINT8_(0x2)                                         /* (AC_WINCTRL) Interrupt on signal below window  */
#define   AC_WINCTRL_WINTSEL0_OUTSIDE_Val     _UINT8_(0x3)                                         /* (AC_WINCTRL) Interrupt on signal outside window  */
#define AC_WINCTRL_WINTSEL0_ABOVE             (AC_WINCTRL_WINTSEL0_ABOVE_Val << AC_WINCTRL_WINTSEL0_Pos) /* (AC_WINCTRL) Interrupt on signal above window Position  */
#define AC_WINCTRL_WINTSEL0_INSIDE            (AC_WINCTRL_WINTSEL0_INSIDE_Val << AC_WINCTRL_WINTSEL0_Pos) /* (AC_WINCTRL) Interrupt on signal inside window Position  */
#define AC_WINCTRL_WINTSEL0_BELOW             (AC_WINCTRL_WINTSEL0_BELOW_Val << AC_WINCTRL_WINTSEL0_Pos) /* (AC_WINCTRL) Interrupt on signal below window Position  */
#define AC_WINCTRL_WINTSEL0_OUTSIDE           (AC_WINCTRL_WINTSEL0_OUTSIDE_Val << AC_WINCTRL_WINTSEL0_Pos) /* (AC_WINCTRL) Interrupt on signal outside window Position  */
#define AC_WINCTRL_WEN1_Pos                   _UINT8_(4)                                           /* (AC_WINCTRL) Window 1 Mode Enable Position */
#define AC_WINCTRL_WEN1_Msk                   (_UINT8_(0x1) << AC_WINCTRL_WEN1_Pos)                /* (AC_WINCTRL) Window 1 Mode Enable Mask */
#define AC_WINCTRL_WEN1(value)                (AC_WINCTRL_WEN1_Msk & (_UINT8_(value) << AC_WINCTRL_WEN1_Pos)) /* Assigment of value for WEN1 in the AC_WINCTRL register */
#define AC_WINCTRL_WINTSEL1_Pos               _UINT8_(5)                                           /* (AC_WINCTRL) Window 1 Interrupt Selection Position */
#define AC_WINCTRL_WINTSEL1_Msk               (_UINT8_(0x3) << AC_WINCTRL_WINTSEL1_Pos)            /* (AC_WINCTRL) Window 1 Interrupt Selection Mask */
#define AC_WINCTRL_WINTSEL1(value)            (AC_WINCTRL_WINTSEL1_Msk & (_UINT8_(value) << AC_WINCTRL_WINTSEL1_Pos)) /* Assigment of value for WINTSEL1 in the AC_WINCTRL register */
#define   AC_WINCTRL_WINTSEL1_ABOVE_Val       _UINT8_(0x0)                                         /* (AC_WINCTRL) Interrupt on signal above window  */
#define   AC_WINCTRL_WINTSEL1_INSIDE_Val      _UINT8_(0x1)                                         /* (AC_WINCTRL) Interrupt on signal inside window  */
#define   AC_WINCTRL_WINTSEL1_BELOW_Val       _UINT8_(0x2)                                         /* (AC_WINCTRL) Interrupt on signal below window  */
#define   AC_WINCTRL_WINTSEL1_OUTSIDE_Val     _UINT8_(0x3)                                         /* (AC_WINCTRL) Interrupt on signal outside window  */
#define AC_WINCTRL_WINTSEL1_ABOVE             (AC_WINCTRL_WINTSEL1_ABOVE_Val << AC_WINCTRL_WINTSEL1_Pos) /* (AC_WINCTRL) Interrupt on signal above window Position  */
#define AC_WINCTRL_WINTSEL1_INSIDE            (AC_WINCTRL_WINTSEL1_INSIDE_Val << AC_WINCTRL_WINTSEL1_Pos) /* (AC_WINCTRL) Interrupt on signal inside window Position  */
#define AC_WINCTRL_WINTSEL1_BELOW             (AC_WINCTRL_WINTSEL1_BELOW_Val << AC_WINCTRL_WINTSEL1_Pos) /* (AC_WINCTRL) Interrupt on signal below window Position  */
#define AC_WINCTRL_WINTSEL1_OUTSIDE           (AC_WINCTRL_WINTSEL1_OUTSIDE_Val << AC_WINCTRL_WINTSEL1_Pos) /* (AC_WINCTRL) Interrupt on signal outside window Position  */
#define AC_WINCTRL_Msk                        _UINT8_(0x77)                                        /* (AC_WINCTRL) Register Mask  */


/* -------- AC_SCALER : (AC Offset: 0x0C) (R/W 8) Scaler n -------- */
#define AC_SCALER_RESETVALUE                  _UINT8_(0x00)                                        /*  (AC_SCALER) Scaler n  Reset Value */

#define AC_SCALER_VALUE_Pos                   _UINT8_(0)                                           /* (AC_SCALER) Scaler Value Position */
#define AC_SCALER_VALUE_Msk                   (_UINT8_(0x3F) << AC_SCALER_VALUE_Pos)               /* (AC_SCALER) Scaler Value Mask */
#define AC_SCALER_VALUE(value)                (AC_SCALER_VALUE_Msk & (_UINT8_(value) << AC_SCALER_VALUE_Pos)) /* Assigment of value for VALUE in the AC_SCALER register */
#define AC_SCALER_Msk                         _UINT8_(0x3F)                                        /* (AC_SCALER) Register Mask  */


/* -------- AC_COMPCTRL : (AC Offset: 0x10) (R/W 32) Comparator Control n -------- */
#define AC_COMPCTRL_RESETVALUE                _UINT32_(0x00)                                       /*  (AC_COMPCTRL) Comparator Control n  Reset Value */

#define AC_COMPCTRL_ENABLE_Pos                _UINT32_(1)                                          /* (AC_COMPCTRL) Enable Position */
#define AC_COMPCTRL_ENABLE_Msk                (_UINT32_(0x1) << AC_COMPCTRL_ENABLE_Pos)            /* (AC_COMPCTRL) Enable Mask */
#define AC_COMPCTRL_ENABLE(value)             (AC_COMPCTRL_ENABLE_Msk & (_UINT32_(value) << AC_COMPCTRL_ENABLE_Pos)) /* Assigment of value for ENABLE in the AC_COMPCTRL register */
#define AC_COMPCTRL_SINGLE_Pos                _UINT32_(2)                                          /* (AC_COMPCTRL) Single-Shot Mode Position */
#define AC_COMPCTRL_SINGLE_Msk                (_UINT32_(0x1) << AC_COMPCTRL_SINGLE_Pos)            /* (AC_COMPCTRL) Single-Shot Mode Mask */
#define AC_COMPCTRL_SINGLE(value)             (AC_COMPCTRL_SINGLE_Msk & (_UINT32_(value) << AC_COMPCTRL_SINGLE_Pos)) /* Assigment of value for SINGLE in the AC_COMPCTRL register */
#define AC_COMPCTRL_INTSEL_Pos                _UINT32_(3)                                          /* (AC_COMPCTRL) Interrupt Selection Position */
#define AC_COMPCTRL_INTSEL_Msk                (_UINT32_(0x3) << AC_COMPCTRL_INTSEL_Pos)            /* (AC_COMPCTRL) Interrupt Selection Mask */
#define AC_COMPCTRL_INTSEL(value)             (AC_COMPCTRL_INTSEL_Msk & (_UINT32_(value) << AC_COMPCTRL_INTSEL_Pos)) /* Assigment of value for INTSEL in the AC_COMPCTRL register */
#define   AC_COMPCTRL_INTSEL_TOGGLE_Val       _UINT32_(0x0)                                        /* (AC_COMPCTRL) Interrupt on comparator output toggle  */
#define   AC_COMPCTRL_INTSEL_RISING_Val       _UINT32_(0x1)                                        /* (AC_COMPCTRL) Interrupt on comparator output rising  */
#define   AC_COMPCTRL_INTSEL_FALLING_Val      _UINT32_(0x2)                                        /* (AC_COMPCTRL) Interrupt on comparator output falling  */
#define   AC_COMPCTRL_INTSEL_EOC_Val          _UINT32_(0x3)                                        /* (AC_COMPCTRL) Interrupt on end of comparison (single-shot mode only)  */
#define AC_COMPCTRL_INTSEL_TOGGLE             (AC_COMPCTRL_INTSEL_TOGGLE_Val << AC_COMPCTRL_INTSEL_Pos) /* (AC_COMPCTRL) Interrupt on comparator output toggle Position  */
#define AC_COMPCTRL_INTSEL_RISING             (AC_COMPCTRL_INTSEL_RISING_Val << AC_COMPCTRL_INTSEL_Pos) /* (AC_COMPCTRL) Interrupt on comparator output rising Position  */
#define AC_COMPCTRL_INTSEL_FALLING            (AC_COMPCTRL_INTSEL_FALLING_Val << AC_COMPCTRL_INTSEL_Pos) /* (AC_COMPCTRL) Interrupt on comparator output falling Position  */
#define AC_COMPCTRL_INTSEL_EOC                (AC_COMPCTRL_INTSEL_EOC_Val << AC_COMPCTRL_INTSEL_Pos) /* (AC_COMPCTRL) Interrupt on end of comparison (single-shot mode only) Position  */
#define AC_COMPCTRL_RUNSTDBY_Pos              _UINT32_(6)                                          /* (AC_COMPCTRL) Run in Standby Position */
#define AC_COMPCTRL_RUNSTDBY_Msk              (_UINT32_(0x1) << AC_COMPCTRL_RUNSTDBY_Pos)          /* (AC_COMPCTRL) Run in Standby Mask */
#define AC_COMPCTRL_RUNSTDBY(value)           (AC_COMPCTRL_RUNSTDBY_Msk & (_UINT32_(value) << AC_COMPCTRL_RUNSTDBY_Pos)) /* Assigment of value for RUNSTDBY in the AC_COMPCTRL register */
#define AC_COMPCTRL_MUXNEG_Pos                _UINT32_(8)                                          /* (AC_COMPCTRL) Negative Input Mux Selection Position */
#define AC_COMPCTRL_MUXNEG_Msk                (_UINT32_(0x7) << AC_COMPCTRL_MUXNEG_Pos)            /* (AC_COMPCTRL) Negative Input Mux Selection Mask */
#define AC_COMPCTRL_MUXNEG(value)             (AC_COMPCTRL_MUXNEG_Msk & (_UINT32_(value) << AC_COMPCTRL_MUXNEG_Pos)) /* Assigment of value for MUXNEG in the AC_COMPCTRL register */
#define   AC_COMPCTRL_MUXNEG_AIN0_Val         _UINT32_(0x0)                                        /* (AC_COMPCTRL) I/O pin 0 for COMPCTRL0/1  */
#define   AC_COMPCTRL_MUXNEG_AIN4_Val         _UINT32_(0x0)                                        /* (AC_COMPCTRL) I/O pin 0 for COMPCTRL2/3  */
#define   AC_COMPCTRL_MUXNEG_AIN1_Val         _UINT32_(0x1)                                        /* (AC_COMPCTRL) I/O pin 1 for COMPCTRL0/1  */
#define   AC_COMPCTRL_MUXNEG_AIN5_Val         _UINT32_(0x1)                                        /* (AC_COMPCTRL) I/O pin 1 for COMPCTRL2/3  */
#define   AC_COMPCTRL_MUXNEG_AIN2_Val         _UINT32_(0x2)                                        /* (AC_COMPCTRL) I/O pin 2 for COMPCTRL0/1  */
#define   AC_COMPCTRL_MUXNEG_AIN6_Val         _UINT32_(0x2)                                        /* (AC_COMPCTRL) I/O pin 2 for COMPCTRL2/3  */
#define   AC_COMPCTRL_MUXNEG_AIN3_Val         _UINT32_(0x3)                                        /* (AC_COMPCTRL) I/O pin 3 for COMPCTRL0/1  */
#define   AC_COMPCTRL_MUXNEG_AIN7_Val         _UINT32_(0x3)                                        /* (AC_COMPCTRL) I/O pin 3 for COMPCTRL2/3  */
#define   AC_COMPCTRL_MUXNEG_AVSS_Val         _UINT32_(0x4)                                        /* (AC_COMPCTRL) Ground  */
#define   AC_COMPCTRL_MUXNEG_VSCALE_Val       _UINT32_(0x5)                                        /* (AC_COMPCTRL) AVDD Scaler  */
#define   AC_COMPCTRL_MUXNEG_BANDGAP_Val      _UINT32_(0x6)                                        /* (AC_COMPCTRL) Internal Bandgap Voltage  */
#define   AC_COMPCTRL_MUXNEG_DAC_Val          _UINT32_(0x7)                                        /* (AC_COMPCTRL) DAC Voltage Output 0 for COMPCTRL0/2  */
#define   AC_COMPCTRL_MUXNEG_OPAMP2_Val       _UINT32_(0x7)                                        /* (AC_COMPCTRL) OPAMP2 Output for COMPCTRL1/3  */
#define AC_COMPCTRL_MUXNEG_AIN0               (AC_COMPCTRL_MUXNEG_AIN0_Val << AC_COMPCTRL_MUXNEG_Pos) /* (AC_COMPCTRL) I/O pin 0 for COMPCTRL0/1 Position  */
#define AC_COMPCTRL_MUXNEG_AIN4               (AC_COMPCTRL_MUXNEG_AIN4_Val << AC_COMPCTRL_MUXNEG_Pos) /* (AC_COMPCTRL) I/O pin 0 for COMPCTRL2/3 Position  */
#define AC_COMPCTRL_MUXNEG_AIN1               (AC_COMPCTRL_MUXNEG_AIN1_Val << AC_COMPCTRL_MUXNEG_Pos) /* (AC_COMPCTRL) I/O pin 1 for COMPCTRL0/1 Position  */
#define AC_COMPCTRL_MUXNEG_AIN5               (AC_COMPCTRL_MUXNEG_AIN5_Val << AC_COMPCTRL_MUXNEG_Pos) /* (AC_COMPCTRL) I/O pin 1 for COMPCTRL2/3 Position  */
#define AC_COMPCTRL_MUXNEG_AIN2               (AC_COMPCTRL_MUXNEG_AIN2_Val << AC_COMPCTRL_MUXNEG_Pos) /* (AC_COMPCTRL) I/O pin 2 for COMPCTRL0/1 Position  */
#define AC_COMPCTRL_MUXNEG_AIN6               (AC_COMPCTRL_MUXNEG_AIN6_Val << AC_COMPCTRL_MUXNEG_Pos) /* (AC_COMPCTRL) I/O pin 2 for COMPCTRL2/3 Position  */
#define AC_COMPCTRL_MUXNEG_AIN3               (AC_COMPCTRL_MUXNEG_AIN3_Val << AC_COMPCTRL_MUXNEG_Pos) /* (AC_COMPCTRL) I/O pin 3 for COMPCTRL0/1 Position  */
#define AC_COMPCTRL_MUXNEG_AIN7               (AC_COMPCTRL_MUXNEG_AIN7_Val << AC_COMPCTRL_MUXNEG_Pos) /* (AC_COMPCTRL) I/O pin 3 for COMPCTRL2/3 Position  */
#define AC_COMPCTRL_MUXNEG_AVSS               (AC_COMPCTRL_MUXNEG_AVSS_Val << AC_COMPCTRL_MUXNEG_Pos) /* (AC_COMPCTRL) Ground Position  */
#define AC_COMPCTRL_MUXNEG_VSCALE             (AC_COMPCTRL_MUXNEG_VSCALE_Val << AC_COMPCTRL_MUXNEG_Pos) /* (AC_COMPCTRL) AVDD Scaler Position  */
#define AC_COMPCTRL_MUXNEG_BANDGAP            (AC_COMPCTRL_MUXNEG_BANDGAP_Val << AC_COMPCTRL_MUXNEG_Pos) /* (AC_COMPCTRL) Internal Bandgap Voltage Position  */
#define AC_COMPCTRL_MUXNEG_DAC                (AC_COMPCTRL_MUXNEG_DAC_Val << AC_COMPCTRL_MUXNEG_Pos) /* (AC_COMPCTRL) DAC Voltage Output 0 for COMPCTRL0/2 Position  */
#define AC_COMPCTRL_MUXNEG_OPAMP2             (AC_COMPCTRL_MUXNEG_OPAMP2_Val << AC_COMPCTRL_MUXNEG_Pos) /* (AC_COMPCTRL) OPAMP2 Output for COMPCTRL1/3 Position  */
#define AC_COMPCTRL_MUXPOS_Pos                _UINT32_(12)                                         /* (AC_COMPCTRL) Positive Input Mux Selection Position */
#define AC_COMPCTRL_MUXPOS_Msk                (_UINT32_(0x7) << AC_COMPCTRL_MUXPOS_Pos)            /* (AC_COMPCTRL) Positive Input Mux Selection Mask */
#define AC_COMPCTRL_MUXPOS(value)             (AC_COMPCTRL_MUXPOS_Msk & (_UINT32_(value) << AC_COMPCTRL_MUXPOS_Pos)) /* Assigment of value for MUXPOS in the AC_COMPCTRL register */
#define   AC_COMPCTRL_MUXPOS_AIN0_Val         _UINT32_(0x0)                                        /* (AC_COMPCTRL) I/O pin 0 for COMPCTRL0/1  */
#define   AC_COMPCTRL_MUXPOS_AIN4_Val         _UINT32_(0x0)                                        /* (AC_COMPCTRL) I/O pin 0 for COMPCTRL2/3  */
#define   AC_COMPCTRL_MUXPOS_AIN1_Val         _UINT32_(0x1)                                        /* (AC_COMPCTRL) I/O pin 1 for COMPCTRL0/1  */
#define   AC_COMPCTRL_MUXPOS_AIN5_Val         _UINT32_(0x1)                                        /* (AC_COMPCTRL) I/O pin 1 for COMPCTRL2/3  */
#define   AC_COMPCTRL_MUXPOS_AIN2_Val         _UINT32_(0x2)                                        /* (AC_COMPCTRL) I/O pin 2 for COMPCTRL0/1  */
#define   AC_COMPCTRL_MUXPOS_AIN6_Val         _UINT32_(0x2)                                        /* (AC_COMPCTRL) I/O pin 2 for COMPCTRL2/3  */
#define   AC_COMPCTRL_MUXPOS_AIN3_Val         _UINT32_(0x3)                                        /* (AC_COMPCTRL) I/O pin 3 for COMPCTRL0/1  */
#define   AC_COMPCTRL_MUXPOS_AIN7_Val         _UINT32_(0x3)                                        /* (AC_COMPCTRL) I/O pin 3 for COMPCTRL2/3  */
#define   AC_COMPCTRL_MUXPOS_VSCALE_Val       _UINT32_(0x4)                                        /* (AC_COMPCTRL) AVDD Scaler  */
#define AC_COMPCTRL_MUXPOS_AIN0               (AC_COMPCTRL_MUXPOS_AIN0_Val << AC_COMPCTRL_MUXPOS_Pos) /* (AC_COMPCTRL) I/O pin 0 for COMPCTRL0/1 Position  */
#define AC_COMPCTRL_MUXPOS_AIN4               (AC_COMPCTRL_MUXPOS_AIN4_Val << AC_COMPCTRL_MUXPOS_Pos) /* (AC_COMPCTRL) I/O pin 0 for COMPCTRL2/3 Position  */
#define AC_COMPCTRL_MUXPOS_AIN1               (AC_COMPCTRL_MUXPOS_AIN1_Val << AC_COMPCTRL_MUXPOS_Pos) /* (AC_COMPCTRL) I/O pin 1 for COMPCTRL0/1 Position  */
#define AC_COMPCTRL_MUXPOS_AIN5               (AC_COMPCTRL_MUXPOS_AIN5_Val << AC_COMPCTRL_MUXPOS_Pos) /* (AC_COMPCTRL) I/O pin 1 for COMPCTRL2/3 Position  */
#define AC_COMPCTRL_MUXPOS_AIN2               (AC_COMPCTRL_MUXPOS_AIN2_Val << AC_COMPCTRL_MUXPOS_Pos) /* (AC_COMPCTRL) I/O pin 2 for COMPCTRL0/1 Position  */
#define AC_COMPCTRL_MUXPOS_AIN6               (AC_COMPCTRL_MUXPOS_AIN6_Val << AC_COMPCTRL_MUXPOS_Pos) /* (AC_COMPCTRL) I/O pin 2 for COMPCTRL2/3 Position  */
#define AC_COMPCTRL_MUXPOS_AIN3               (AC_COMPCTRL_MUXPOS_AIN3_Val << AC_COMPCTRL_MUXPOS_Pos) /* (AC_COMPCTRL) I/O pin 3 for COMPCTRL0/1 Position  */
#define AC_COMPCTRL_MUXPOS_AIN7               (AC_COMPCTRL_MUXPOS_AIN7_Val << AC_COMPCTRL_MUXPOS_Pos) /* (AC_COMPCTRL) I/O pin 3 for COMPCTRL2/3 Position  */
#define AC_COMPCTRL_MUXPOS_VSCALE             (AC_COMPCTRL_MUXPOS_VSCALE_Val << AC_COMPCTRL_MUXPOS_Pos) /* (AC_COMPCTRL) AVDD Scaler Position  */
#define AC_COMPCTRL_SWAP_Pos                  _UINT32_(15)                                         /* (AC_COMPCTRL) Swap Inputs and Invert Position */
#define AC_COMPCTRL_SWAP_Msk                  (_UINT32_(0x1) << AC_COMPCTRL_SWAP_Pos)              /* (AC_COMPCTRL) Swap Inputs and Invert Mask */
#define AC_COMPCTRL_SWAP(value)               (AC_COMPCTRL_SWAP_Msk & (_UINT32_(value) << AC_COMPCTRL_SWAP_Pos)) /* Assigment of value for SWAP in the AC_COMPCTRL register */
#define AC_COMPCTRL_SPEED_Pos                 _UINT32_(16)                                         /* (AC_COMPCTRL) Speed Selection Position */
#define AC_COMPCTRL_SPEED_Msk                 (_UINT32_(0x3) << AC_COMPCTRL_SPEED_Pos)             /* (AC_COMPCTRL) Speed Selection Mask */
#define AC_COMPCTRL_SPEED(value)              (AC_COMPCTRL_SPEED_Msk & (_UINT32_(value) << AC_COMPCTRL_SPEED_Pos)) /* Assigment of value for SPEED in the AC_COMPCTRL register */
#define   AC_COMPCTRL_SPEED_LOW_Val           _UINT32_(0x0)                                        /* (AC_COMPCTRL) Low speed  */
#define   AC_COMPCTRL_SPEED_MEDLOW_Val        _UINT32_(0x1)                                        /* (AC_COMPCTRL) Medium low speed  */
#define   AC_COMPCTRL_SPEED_MEDHIGH_Val       _UINT32_(0x2)                                        /* (AC_COMPCTRL) Medium high speed  */
#define   AC_COMPCTRL_SPEED_HIGH_Val          _UINT32_(0x3)                                        /* (AC_COMPCTRL) High speed  */
#define AC_COMPCTRL_SPEED_LOW                 (AC_COMPCTRL_SPEED_LOW_Val << AC_COMPCTRL_SPEED_Pos) /* (AC_COMPCTRL) Low speed Position  */
#define AC_COMPCTRL_SPEED_MEDLOW              (AC_COMPCTRL_SPEED_MEDLOW_Val << AC_COMPCTRL_SPEED_Pos) /* (AC_COMPCTRL) Medium low speed Position  */
#define AC_COMPCTRL_SPEED_MEDHIGH             (AC_COMPCTRL_SPEED_MEDHIGH_Val << AC_COMPCTRL_SPEED_Pos) /* (AC_COMPCTRL) Medium high speed Position  */
#define AC_COMPCTRL_SPEED_HIGH                (AC_COMPCTRL_SPEED_HIGH_Val << AC_COMPCTRL_SPEED_Pos) /* (AC_COMPCTRL) High speed Position  */
#define AC_COMPCTRL_HYSTEN_Pos                _UINT32_(19)                                         /* (AC_COMPCTRL) Hysteresis Enable Position */
#define AC_COMPCTRL_HYSTEN_Msk                (_UINT32_(0x1) << AC_COMPCTRL_HYSTEN_Pos)            /* (AC_COMPCTRL) Hysteresis Enable Mask */
#define AC_COMPCTRL_HYSTEN(value)             (AC_COMPCTRL_HYSTEN_Msk & (_UINT32_(value) << AC_COMPCTRL_HYSTEN_Pos)) /* Assigment of value for HYSTEN in the AC_COMPCTRL register */
#define AC_COMPCTRL_HYST_Pos                  _UINT32_(20)                                         /* (AC_COMPCTRL) Hysteresis Level Position */
#define AC_COMPCTRL_HYST_Msk                  (_UINT32_(0x3) << AC_COMPCTRL_HYST_Pos)              /* (AC_COMPCTRL) Hysteresis Level Mask */
#define AC_COMPCTRL_HYST(value)               (AC_COMPCTRL_HYST_Msk & (_UINT32_(value) << AC_COMPCTRL_HYST_Pos)) /* Assigment of value for HYST in the AC_COMPCTRL register */
#define   AC_COMPCTRL_HYST_HYST50_Val         _UINT32_(0x0)                                        /* (AC_COMPCTRL) 50mV  */
#define   AC_COMPCTRL_HYST_HYST70_Val         _UINT32_(0x1)                                        /* (AC_COMPCTRL) 70mV  */
#define   AC_COMPCTRL_HYST_HYST90_Val         _UINT32_(0x2)                                        /* (AC_COMPCTRL) 90mV  */
#define   AC_COMPCTRL_HYST_HYST110_Val        _UINT32_(0x3)                                        /* (AC_COMPCTRL) 110mV  */
#define AC_COMPCTRL_HYST_HYST50               (AC_COMPCTRL_HYST_HYST50_Val << AC_COMPCTRL_HYST_Pos) /* (AC_COMPCTRL) 50mV Position  */
#define AC_COMPCTRL_HYST_HYST70               (AC_COMPCTRL_HYST_HYST70_Val << AC_COMPCTRL_HYST_Pos) /* (AC_COMPCTRL) 70mV Position  */
#define AC_COMPCTRL_HYST_HYST90               (AC_COMPCTRL_HYST_HYST90_Val << AC_COMPCTRL_HYST_Pos) /* (AC_COMPCTRL) 90mV Position  */
#define AC_COMPCTRL_HYST_HYST110              (AC_COMPCTRL_HYST_HYST110_Val << AC_COMPCTRL_HYST_Pos) /* (AC_COMPCTRL) 110mV Position  */
#define AC_COMPCTRL_FLEN_Pos                  _UINT32_(24)                                         /* (AC_COMPCTRL) Filter Length Position */
#define AC_COMPCTRL_FLEN_Msk                  (_UINT32_(0x7) << AC_COMPCTRL_FLEN_Pos)              /* (AC_COMPCTRL) Filter Length Mask */
#define AC_COMPCTRL_FLEN(value)               (AC_COMPCTRL_FLEN_Msk & (_UINT32_(value) << AC_COMPCTRL_FLEN_Pos)) /* Assigment of value for FLEN in the AC_COMPCTRL register */
#define   AC_COMPCTRL_FLEN_OFF_Val            _UINT32_(0x0)                                        /* (AC_COMPCTRL) No filtering  */
#define   AC_COMPCTRL_FLEN_MAJ3_Val           _UINT32_(0x1)                                        /* (AC_COMPCTRL) 3-bit majority function (2 of 3)  */
#define   AC_COMPCTRL_FLEN_MAJ5_Val           _UINT32_(0x2)                                        /* (AC_COMPCTRL) 5-bit majority function (3 of 5)  */
#define AC_COMPCTRL_FLEN_OFF                  (AC_COMPCTRL_FLEN_OFF_Val << AC_COMPCTRL_FLEN_Pos)   /* (AC_COMPCTRL) No filtering Position  */
#define AC_COMPCTRL_FLEN_MAJ3                 (AC_COMPCTRL_FLEN_MAJ3_Val << AC_COMPCTRL_FLEN_Pos)  /* (AC_COMPCTRL) 3-bit majority function (2 of 3) Position  */
#define AC_COMPCTRL_FLEN_MAJ5                 (AC_COMPCTRL_FLEN_MAJ5_Val << AC_COMPCTRL_FLEN_Pos)  /* (AC_COMPCTRL) 5-bit majority function (3 of 5) Position  */
#define AC_COMPCTRL_OUT_Pos                   _UINT32_(28)                                         /* (AC_COMPCTRL) Output Position */
#define AC_COMPCTRL_OUT_Msk                   (_UINT32_(0x3) << AC_COMPCTRL_OUT_Pos)               /* (AC_COMPCTRL) Output Mask */
#define AC_COMPCTRL_OUT(value)                (AC_COMPCTRL_OUT_Msk & (_UINT32_(value) << AC_COMPCTRL_OUT_Pos)) /* Assigment of value for OUT in the AC_COMPCTRL register */
#define   AC_COMPCTRL_OUT_OFF_Val             _UINT32_(0x0)                                        /* (AC_COMPCTRL) The output of COMPn is not routed to the COMPn I/O port  */
#define   AC_COMPCTRL_OUT_ASYNC_Val           _UINT32_(0x1)                                        /* (AC_COMPCTRL) The asynchronous output of COMPn is routed to the COMPn I/O port  */
#define   AC_COMPCTRL_OUT_SYNC_Val            _UINT32_(0x2)                                        /* (AC_COMPCTRL) The synchronous output (including filtering) of COMPn is routed to the COMPn I/O port  */
#define AC_COMPCTRL_OUT_OFF                   (AC_COMPCTRL_OUT_OFF_Val << AC_COMPCTRL_OUT_Pos)     /* (AC_COMPCTRL) The output of COMPn is not routed to the COMPn I/O port Position  */
#define AC_COMPCTRL_OUT_ASYNC                 (AC_COMPCTRL_OUT_ASYNC_Val << AC_COMPCTRL_OUT_Pos)   /* (AC_COMPCTRL) The asynchronous output of COMPn is routed to the COMPn I/O port Position  */
#define AC_COMPCTRL_OUT_SYNC                  (AC_COMPCTRL_OUT_SYNC_Val << AC_COMPCTRL_OUT_Pos)    /* (AC_COMPCTRL) The synchronous output (including filtering) of COMPn is routed to the COMPn I/O port Position  */
#define AC_COMPCTRL_Msk                       _UINT32_(0x373BF75E)                                 /* (AC_COMPCTRL) Register Mask  */


/* -------- AC_SYNCBUSY : (AC Offset: 0x20) ( R/ 32) Synchronization Busy -------- */
#define AC_SYNCBUSY_RESETVALUE                _UINT32_(0x00)                                       /*  (AC_SYNCBUSY) Synchronization Busy  Reset Value */

#define AC_SYNCBUSY_SWRST_Pos                 _UINT32_(0)                                          /* (AC_SYNCBUSY) Software Reset Synchronization Busy Position */
#define AC_SYNCBUSY_SWRST_Msk                 (_UINT32_(0x1) << AC_SYNCBUSY_SWRST_Pos)             /* (AC_SYNCBUSY) Software Reset Synchronization Busy Mask */
#define AC_SYNCBUSY_SWRST(value)              (AC_SYNCBUSY_SWRST_Msk & (_UINT32_(value) << AC_SYNCBUSY_SWRST_Pos)) /* Assigment of value for SWRST in the AC_SYNCBUSY register */
#define AC_SYNCBUSY_ENABLE_Pos                _UINT32_(1)                                          /* (AC_SYNCBUSY) Enable Synchronization Busy Position */
#define AC_SYNCBUSY_ENABLE_Msk                (_UINT32_(0x1) << AC_SYNCBUSY_ENABLE_Pos)            /* (AC_SYNCBUSY) Enable Synchronization Busy Mask */
#define AC_SYNCBUSY_ENABLE(value)             (AC_SYNCBUSY_ENABLE_Msk & (_UINT32_(value) << AC_SYNCBUSY_ENABLE_Pos)) /* Assigment of value for ENABLE in the AC_SYNCBUSY register */
#define AC_SYNCBUSY_WINCTRL_Pos               _UINT32_(2)                                          /* (AC_SYNCBUSY) WINCTRL Synchronization Busy Position */
#define AC_SYNCBUSY_WINCTRL_Msk               (_UINT32_(0x1) << AC_SYNCBUSY_WINCTRL_Pos)           /* (AC_SYNCBUSY) WINCTRL Synchronization Busy Mask */
#define AC_SYNCBUSY_WINCTRL(value)            (AC_SYNCBUSY_WINCTRL_Msk & (_UINT32_(value) << AC_SYNCBUSY_WINCTRL_Pos)) /* Assigment of value for WINCTRL in the AC_SYNCBUSY register */
#define AC_SYNCBUSY_COMPCTRL0_Pos             _UINT32_(3)                                          /* (AC_SYNCBUSY) COMPCTRL 0 Synchronization Busy Position */
#define AC_SYNCBUSY_COMPCTRL0_Msk             (_UINT32_(0x1) << AC_SYNCBUSY_COMPCTRL0_Pos)         /* (AC_SYNCBUSY) COMPCTRL 0 Synchronization Busy Mask */
#define AC_SYNCBUSY_COMPCTRL0(value)          (AC_SYNCBUSY_COMPCTRL0_Msk & (_UINT32_(value) << AC_SYNCBUSY_COMPCTRL0_Pos)) /* Assigment of value for COMPCTRL0 in the AC_SYNCBUSY register */
#define AC_SYNCBUSY_COMPCTRL1_Pos             _UINT32_(4)                                          /* (AC_SYNCBUSY) COMPCTRL 1 Synchronization Busy Position */
#define AC_SYNCBUSY_COMPCTRL1_Msk             (_UINT32_(0x1) << AC_SYNCBUSY_COMPCTRL1_Pos)         /* (AC_SYNCBUSY) COMPCTRL 1 Synchronization Busy Mask */
#define AC_SYNCBUSY_COMPCTRL1(value)          (AC_SYNCBUSY_COMPCTRL1_Msk & (_UINT32_(value) << AC_SYNCBUSY_COMPCTRL1_Pos)) /* Assigment of value for COMPCTRL1 in the AC_SYNCBUSY register */
#define AC_SYNCBUSY_COMPCTRL2_Pos             _UINT32_(5)                                          /* (AC_SYNCBUSY) COMPCTRL 2 Synchronization Busy Position */
#define AC_SYNCBUSY_COMPCTRL2_Msk             (_UINT32_(0x1) << AC_SYNCBUSY_COMPCTRL2_Pos)         /* (AC_SYNCBUSY) COMPCTRL 2 Synchronization Busy Mask */
#define AC_SYNCBUSY_COMPCTRL2(value)          (AC_SYNCBUSY_COMPCTRL2_Msk & (_UINT32_(value) << AC_SYNCBUSY_COMPCTRL2_Pos)) /* Assigment of value for COMPCTRL2 in the AC_SYNCBUSY register */
#define AC_SYNCBUSY_COMPCTRL3_Pos             _UINT32_(6)                                          /* (AC_SYNCBUSY) COMPCTRL 3 Synchronization Busy Position */
#define AC_SYNCBUSY_COMPCTRL3_Msk             (_UINT32_(0x1) << AC_SYNCBUSY_COMPCTRL3_Pos)         /* (AC_SYNCBUSY) COMPCTRL 3 Synchronization Busy Mask */
#define AC_SYNCBUSY_COMPCTRL3(value)          (AC_SYNCBUSY_COMPCTRL3_Msk & (_UINT32_(value) << AC_SYNCBUSY_COMPCTRL3_Pos)) /* Assigment of value for COMPCTRL3 in the AC_SYNCBUSY register */
#define AC_SYNCBUSY_Msk                       _UINT32_(0x0000007F)                                 /* (AC_SYNCBUSY) Register Mask  */

#define AC_SYNCBUSY_COMPCTRL_Pos              _UINT32_(3)                                          /* (AC_SYNCBUSY Position) COMPCTRL 3 Synchronization Busy */
#define AC_SYNCBUSY_COMPCTRL_Msk              (_UINT32_(0xF) << AC_SYNCBUSY_COMPCTRL_Pos)          /* (AC_SYNCBUSY Mask) COMPCTRL */
#define AC_SYNCBUSY_COMPCTRL(value)           (AC_SYNCBUSY_COMPCTRL_Msk & (_UINT32_(value) << AC_SYNCBUSY_COMPCTRL_Pos)) 

/** \brief AC register offsets definitions */
#define AC_CTRLA_REG_OFST              _UINT32_(0x00)      /* (AC_CTRLA) Control A Offset */
#define AC_CTRLB_REG_OFST              _UINT32_(0x01)      /* (AC_CTRLB) Control B Offset */
#define AC_EVCTRL_REG_OFST             _UINT32_(0x02)      /* (AC_EVCTRL) Event Control Offset */
#define AC_INTENCLR_REG_OFST           _UINT32_(0x04)      /* (AC_INTENCLR) Interrupt Enable Clear Offset */
#define AC_INTENSET_REG_OFST           _UINT32_(0x05)      /* (AC_INTENSET) Interrupt Enable Set Offset */
#define AC_INTFLAG_REG_OFST            _UINT32_(0x06)      /* (AC_INTFLAG) Interrupt Flag Status and Clear Offset */
#define AC_STATUSA_REG_OFST            _UINT32_(0x07)      /* (AC_STATUSA) Status A Offset */
#define AC_STATUSB_REG_OFST            _UINT32_(0x08)      /* (AC_STATUSB) Status B Offset */
#define AC_DBGCTRL_REG_OFST            _UINT32_(0x09)      /* (AC_DBGCTRL) Debug Control Offset */
#define AC_WINCTRL_REG_OFST            _UINT32_(0x0A)      /* (AC_WINCTRL) Window Control Offset */
#define AC_SCALER_REG_OFST             _UINT32_(0x0C)      /* (AC_SCALER) Scaler n Offset */
#define AC_SCALER0_REG_OFST            _UINT32_(0x0C)      /* (AC_SCALER0) Scaler n Offset */
#define AC_SCALER1_REG_OFST            _UINT32_(0x0D)      /* (AC_SCALER1) Scaler n Offset */
#define AC_SCALER2_REG_OFST            _UINT32_(0x0E)      /* (AC_SCALER2) Scaler n Offset */
#define AC_SCALER3_REG_OFST            _UINT32_(0x0F)      /* (AC_SCALER3) Scaler n Offset */
#define AC_COMPCTRL_REG_OFST           _UINT32_(0x10)      /* (AC_COMPCTRL) Comparator Control n Offset */
#define AC_COMPCTRL0_REG_OFST          _UINT32_(0x10)      /* (AC_COMPCTRL0) Comparator Control n Offset */
#define AC_COMPCTRL1_REG_OFST          _UINT32_(0x14)      /* (AC_COMPCTRL1) Comparator Control n Offset */
#define AC_COMPCTRL2_REG_OFST          _UINT32_(0x18)      /* (AC_COMPCTRL2) Comparator Control n Offset */
#define AC_COMPCTRL3_REG_OFST          _UINT32_(0x1C)      /* (AC_COMPCTRL3) Comparator Control n Offset */
#define AC_SYNCBUSY_REG_OFST           _UINT32_(0x20)      /* (AC_SYNCBUSY) Synchronization Busy Offset */

#if !(defined(__ASSEMBLER__) || defined(__IAR_SYSTEMS_ASM__))
/** \brief AC register API structure */
typedef struct
{  /* Analog Comparators */
  __IO  uint8_t                        AC_CTRLA;           /**< Offset: 0x00 (R/W  8) Control A */
  __IO  uint8_t                        AC_CTRLB;           /**< Offset: 0x01 (R/W  8) Control B */
  __IO  uint16_t                       AC_EVCTRL;          /**< Offset: 0x02 (R/W  16) Event Control */
  __IO  uint8_t                        AC_INTENCLR;        /**< Offset: 0x04 (R/W  8) Interrupt Enable Clear */
  __IO  uint8_t                        AC_INTENSET;        /**< Offset: 0x05 (R/W  8) Interrupt Enable Set */
  __IO  uint8_t                        AC_INTFLAG;         /**< Offset: 0x06 (R/W  8) Interrupt Flag Status and Clear */
  __I   uint8_t                        AC_STATUSA;         /**< Offset: 0x07 (R/   8) Status A */
  __I   uint8_t                        AC_STATUSB;         /**< Offset: 0x08 (R/   8) Status B */
  __IO  uint8_t                        AC_DBGCTRL;         /**< Offset: 0x09 (R/W  8) Debug Control */
  __IO  uint8_t                        AC_WINCTRL;         /**< Offset: 0x0A (R/W  8) Window Control */
  __I   uint8_t                        Reserved1[0x01];
  __IO  uint8_t                        AC_SCALER[4];       /**< Offset: 0x0C (R/W  8) Scaler n */
  __IO  uint32_t                       AC_COMPCTRL[4];     /**< Offset: 0x10 (R/W  32) Comparator Control n */
  __I   uint32_t                       AC_SYNCBUSY;        /**< Offset: 0x20 (R/   32) Synchronization Busy */
} ac_registers_t;


#endif /* !(defined(__ASSEMBLER__) || defined(__IAR_SYSTEMS_ASM__)) */
#endif /* _PIC32CMLE00_AC_COMPONENT_H_ */
