ice458/RPN_Scientific_Calc/src/packs/PIC32CM2532LE00048_DFP/component/adc.h

/*
 * Component description for ADC
 *
 * Copyright (c) 2023 Microchip Technology Inc. and its subsidiaries.
 *
 * Subject to your compliance with these terms, you may use Microchip software and any derivatives
 * exclusively with Microchip products. It is your responsibility to comply with third party license
 * terms applicable to your use of third party software (including open source software) that may
 * accompany Microchip software.
 *
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
 * IN NO EVENT WILL MICROCHIP BE LIABLE FOR ANY INDIRECT, SPECIAL, PUNITIVE, INCIDENTAL OR CONSEQUENTIAL
 * LOSS, DAMAGE, COST OR EXPENSE OF ANY KIND WHATSOEVER RELATED TO THE SOFTWARE, HOWEVER CAUSED, EVEN IF
 * MICROCHIP HAS BEEN ADVISED OF THE POSSIBILITY OR THE DAMAGES ARE FORESEEABLE. TO THE FULLEST EXTENT
 * ALLOWED BY LAW, MICROCHIP'S TOTAL LIABILITY ON ALL CLAIMS IN ANY WAY RELATED TO THIS SOFTWARE WILL NOT
 * EXCEED THE AMOUNT OF FEES, IF ANY, THAT YOU HAVE PAID DIRECTLY TO MICROCHIP FOR THIS SOFTWARE.
 *
 */

/* file generated from device description version 2022-09-09T06:08:26Z */
#ifndef _PIC32CMLE00_ADC_COMPONENT_H_
#define _PIC32CMLE00_ADC_COMPONENT_H_

/* ************************************************************************** */
/*   SOFTWARE API DEFINITION FOR ADC                                          */
/* ************************************************************************** */

/* -------- ADC_CTRLA : (ADC Offset: 0x00) (R/W 8) Control A -------- */
#define ADC_CTRLA_RESETVALUE                  _UINT8_(0x00)                                        /*  (ADC_CTRLA) Control A  Reset Value */

#define ADC_CTRLA_SWRST_Pos                   _UINT8_(0)                                           /* (ADC_CTRLA) Software Reset Position */
#define ADC_CTRLA_SWRST_Msk                   (_UINT8_(0x1) << ADC_CTRLA_SWRST_Pos)                /* (ADC_CTRLA) Software Reset Mask */
#define ADC_CTRLA_SWRST(value)                (ADC_CTRLA_SWRST_Msk & (_UINT8_(value) << ADC_CTRLA_SWRST_Pos)) /* Assigment of value for SWRST in the ADC_CTRLA register */
#define ADC_CTRLA_ENABLE_Pos                  _UINT8_(1)                                           /* (ADC_CTRLA) Enable Position */
#define ADC_CTRLA_ENABLE_Msk                  (_UINT8_(0x1) << ADC_CTRLA_ENABLE_Pos)               /* (ADC_CTRLA) Enable Mask */
#define ADC_CTRLA_ENABLE(value)               (ADC_CTRLA_ENABLE_Msk & (_UINT8_(value) << ADC_CTRLA_ENABLE_Pos)) /* Assigment of value for ENABLE in the ADC_CTRLA register */
#define ADC_CTRLA_RUNSTDBY_Pos                _UINT8_(6)                                           /* (ADC_CTRLA) Run During Standby Position */
#define ADC_CTRLA_RUNSTDBY_Msk                (_UINT8_(0x1) << ADC_CTRLA_RUNSTDBY_Pos)             /* (ADC_CTRLA) Run During Standby Mask */
#define ADC_CTRLA_RUNSTDBY(value)             (ADC_CTRLA_RUNSTDBY_Msk & (_UINT8_(value) << ADC_CTRLA_RUNSTDBY_Pos)) /* Assigment of value for RUNSTDBY in the ADC_CTRLA register */
#define ADC_CTRLA_ONDEMAND_Pos                _UINT8_(7)                                           /* (ADC_CTRLA) On Demand Control Position */
#define ADC_CTRLA_ONDEMAND_Msk                (_UINT8_(0x1) << ADC_CTRLA_ONDEMAND_Pos)             /* (ADC_CTRLA) On Demand Control Mask */
#define ADC_CTRLA_ONDEMAND(value)             (ADC_CTRLA_ONDEMAND_Msk & (_UINT8_(value) << ADC_CTRLA_ONDEMAND_Pos)) /* Assigment of value for ONDEMAND in the ADC_CTRLA register */
#define ADC_CTRLA_Msk                         _UINT8_(0xC3)                                        /* (ADC_CTRLA) Register Mask  */


/* -------- ADC_CTRLB : (ADC Offset: 0x01) (R/W 8) Control B -------- */
#define ADC_CTRLB_RESETVALUE                  _UINT8_(0x00)                                        /*  (ADC_CTRLB) Control B  Reset Value */

#define ADC_CTRLB_PRESCALER_Pos               _UINT8_(0)                                           /* (ADC_CTRLB) Prescaler Configuration Position */
#define ADC_CTRLB_PRESCALER_Msk               (_UINT8_(0x7) << ADC_CTRLB_PRESCALER_Pos)            /* (ADC_CTRLB) Prescaler Configuration Mask */
#define ADC_CTRLB_PRESCALER(value)            (ADC_CTRLB_PRESCALER_Msk & (_UINT8_(value) << ADC_CTRLB_PRESCALER_Pos)) /* Assigment of value for PRESCALER in the ADC_CTRLB register */
#define   ADC_CTRLB_PRESCALER_DIV2_Val        _UINT8_(0x0)                                         /* (ADC_CTRLB) Peripheral clock divided by 2  */
#define   ADC_CTRLB_PRESCALER_DIV4_Val        _UINT8_(0x1)                                         /* (ADC_CTRLB) Peripheral clock divided by 4  */
#define   ADC_CTRLB_PRESCALER_DIV8_Val        _UINT8_(0x2)                                         /* (ADC_CTRLB) Peripheral clock divided by 8  */
#define   ADC_CTRLB_PRESCALER_DIV16_Val       _UINT8_(0x3)                                         /* (ADC_CTRLB) Peripheral clock divided by 16  */
#define   ADC_CTRLB_PRESCALER_DIV32_Val       _UINT8_(0x4)                                         /* (ADC_CTRLB) Peripheral clock divided by 32  */
#define   ADC_CTRLB_PRESCALER_DIV64_Val       _UINT8_(0x5)                                         /* (ADC_CTRLB) Peripheral clock divided by 64  */
#define   ADC_CTRLB_PRESCALER_DIV128_Val      _UINT8_(0x6)                                         /* (ADC_CTRLB) Peripheral clock divided by 128  */
#define   ADC_CTRLB_PRESCALER_DIV256_Val      _UINT8_(0x7)                                         /* (ADC_CTRLB) Peripheral clock divided by 256  */
#define ADC_CTRLB_PRESCALER_DIV2              (ADC_CTRLB_PRESCALER_DIV2_Val << ADC_CTRLB_PRESCALER_Pos) /* (ADC_CTRLB) Peripheral clock divided by 2 Position  */
#define ADC_CTRLB_PRESCALER_DIV4              (ADC_CTRLB_PRESCALER_DIV4_Val << ADC_CTRLB_PRESCALER_Pos) /* (ADC_CTRLB) Peripheral clock divided by 4 Position  */
#define ADC_CTRLB_PRESCALER_DIV8              (ADC_CTRLB_PRESCALER_DIV8_Val << ADC_CTRLB_PRESCALER_Pos) /* (ADC_CTRLB) Peripheral clock divided by 8 Position  */
#define ADC_CTRLB_PRESCALER_DIV16             (ADC_CTRLB_PRESCALER_DIV16_Val << ADC_CTRLB_PRESCALER_Pos) /* (ADC_CTRLB) Peripheral clock divided by 16 Position  */
#define ADC_CTRLB_PRESCALER_DIV32             (ADC_CTRLB_PRESCALER_DIV32_Val << ADC_CTRLB_PRESCALER_Pos) /* (ADC_CTRLB) Peripheral clock divided by 32 Position  */
#define ADC_CTRLB_PRESCALER_DIV64             (ADC_CTRLB_PRESCALER_DIV64_Val << ADC_CTRLB_PRESCALER_Pos) /* (ADC_CTRLB) Peripheral clock divided by 64 Position  */
#define ADC_CTRLB_PRESCALER_DIV128            (ADC_CTRLB_PRESCALER_DIV128_Val << ADC_CTRLB_PRESCALER_Pos) /* (ADC_CTRLB) Peripheral clock divided by 128 Position  */
#define ADC_CTRLB_PRESCALER_DIV256            (ADC_CTRLB_PRESCALER_DIV256_Val << ADC_CTRLB_PRESCALER_Pos) /* (ADC_CTRLB) Peripheral clock divided by 256 Position  */
#define ADC_CTRLB_Msk                         _UINT8_(0x07)                                        /* (ADC_CTRLB) Register Mask  */


/* -------- ADC_REFCTRL : (ADC Offset: 0x02) (R/W 8) Reference Control -------- */
#define ADC_REFCTRL_RESETVALUE                _UINT8_(0x00)                                        /*  (ADC_REFCTRL) Reference Control  Reset Value */

#define ADC_REFCTRL_REFSEL_Pos                _UINT8_(0)                                           /* (ADC_REFCTRL) Reference Selection Position */
#define ADC_REFCTRL_REFSEL_Msk                (_UINT8_(0xF) << ADC_REFCTRL_REFSEL_Pos)             /* (ADC_REFCTRL) Reference Selection Mask */
#define ADC_REFCTRL_REFSEL(value)             (ADC_REFCTRL_REFSEL_Msk & (_UINT8_(value) << ADC_REFCTRL_REFSEL_Pos)) /* Assigment of value for REFSEL in the ADC_REFCTRL register */
#define   ADC_REFCTRL_REFSEL_INTREF_Val       _UINT8_(0x0)                                         /* (ADC_REFCTRL) Internal Voltage Reference  */
#define   ADC_REFCTRL_REFSEL_INTVCC0_Val      _UINT8_(0x1)                                         /* (ADC_REFCTRL) 1/1.6 AVDD  */
#define   ADC_REFCTRL_REFSEL_INTVCC1_Val      _UINT8_(0x2)                                         /* (ADC_REFCTRL) 1/2 AVDD  */
#define   ADC_REFCTRL_REFSEL_VREFA_Val        _UINT8_(0x3)                                         /* (ADC_REFCTRL) External Voltage Reference A (shared with DAC)  */
#define   ADC_REFCTRL_REFSEL_VREFB_Val        _UINT8_(0x4)                                         /* (ADC_REFCTRL) External Voltage Reference B  */
#define   ADC_REFCTRL_REFSEL_INTVCC2_Val      _UINT8_(0x5)                                         /* (ADC_REFCTRL) AVDD  */
#define ADC_REFCTRL_REFSEL_INTREF             (ADC_REFCTRL_REFSEL_INTREF_Val << ADC_REFCTRL_REFSEL_Pos) /* (ADC_REFCTRL) Internal Voltage Reference Position  */
#define ADC_REFCTRL_REFSEL_INTVCC0            (ADC_REFCTRL_REFSEL_INTVCC0_Val << ADC_REFCTRL_REFSEL_Pos) /* (ADC_REFCTRL) 1/1.6 AVDD Position  */
#define ADC_REFCTRL_REFSEL_INTVCC1            (ADC_REFCTRL_REFSEL_INTVCC1_Val << ADC_REFCTRL_REFSEL_Pos) /* (ADC_REFCTRL) 1/2 AVDD Position  */
#define ADC_REFCTRL_REFSEL_VREFA              (ADC_REFCTRL_REFSEL_VREFA_Val << ADC_REFCTRL_REFSEL_Pos) /* (ADC_REFCTRL) External Voltage Reference A (shared with DAC) Position  */
#define ADC_REFCTRL_REFSEL_VREFB              (ADC_REFCTRL_REFSEL_VREFB_Val << ADC_REFCTRL_REFSEL_Pos) /* (ADC_REFCTRL) External Voltage Reference B Position  */
#define ADC_REFCTRL_REFSEL_INTVCC2            (ADC_REFCTRL_REFSEL_INTVCC2_Val << ADC_REFCTRL_REFSEL_Pos) /* (ADC_REFCTRL) AVDD Position  */
#define ADC_REFCTRL_REFCOMP_Pos               _UINT8_(7)                                           /* (ADC_REFCTRL) Reference Buffer Offset Compensation Enable Position */
#define ADC_REFCTRL_REFCOMP_Msk               (_UINT8_(0x1) << ADC_REFCTRL_REFCOMP_Pos)            /* (ADC_REFCTRL) Reference Buffer Offset Compensation Enable Mask */
#define ADC_REFCTRL_REFCOMP(value)            (ADC_REFCTRL_REFCOMP_Msk & (_UINT8_(value) << ADC_REFCTRL_REFCOMP_Pos)) /* Assigment of value for REFCOMP in the ADC_REFCTRL register */
#define ADC_REFCTRL_Msk                       _UINT8_(0x8F)                                        /* (ADC_REFCTRL) Register Mask  */


/* -------- ADC_EVCTRL : (ADC Offset: 0x03) (R/W 8) Event Control -------- */
#define ADC_EVCTRL_RESETVALUE                 _UINT8_(0x00)                                        /*  (ADC_EVCTRL) Event Control  Reset Value */

#define ADC_EVCTRL_FLUSHEI_Pos                _UINT8_(0)                                           /* (ADC_EVCTRL) Flush Event Input Enable Position */
#define ADC_EVCTRL_FLUSHEI_Msk                (_UINT8_(0x1) << ADC_EVCTRL_FLUSHEI_Pos)             /* (ADC_EVCTRL) Flush Event Input Enable Mask */
#define ADC_EVCTRL_FLUSHEI(value)             (ADC_EVCTRL_FLUSHEI_Msk & (_UINT8_(value) << ADC_EVCTRL_FLUSHEI_Pos)) /* Assigment of value for FLUSHEI in the ADC_EVCTRL register */
#define ADC_EVCTRL_STARTEI_Pos                _UINT8_(1)                                           /* (ADC_EVCTRL) Start Conversion Event Input Enable Position */
#define ADC_EVCTRL_STARTEI_Msk                (_UINT8_(0x1) << ADC_EVCTRL_STARTEI_Pos)             /* (ADC_EVCTRL) Start Conversion Event Input Enable Mask */
#define ADC_EVCTRL_STARTEI(value)             (ADC_EVCTRL_STARTEI_Msk & (_UINT8_(value) << ADC_EVCTRL_STARTEI_Pos)) /* Assigment of value for STARTEI in the ADC_EVCTRL register */
#define ADC_EVCTRL_FLUSHINV_Pos               _UINT8_(2)                                           /* (ADC_EVCTRL) Flush Event Invert Enable Position */
#define ADC_EVCTRL_FLUSHINV_Msk               (_UINT8_(0x1) << ADC_EVCTRL_FLUSHINV_Pos)            /* (ADC_EVCTRL) Flush Event Invert Enable Mask */
#define ADC_EVCTRL_FLUSHINV(value)            (ADC_EVCTRL_FLUSHINV_Msk & (_UINT8_(value) << ADC_EVCTRL_FLUSHINV_Pos)) /* Assigment of value for FLUSHINV in the ADC_EVCTRL register */
#define ADC_EVCTRL_STARTINV_Pos               _UINT8_(3)                                           /* (ADC_EVCTRL) Start Event Invert Enable Position */
#define ADC_EVCTRL_STARTINV_Msk               (_UINT8_(0x1) << ADC_EVCTRL_STARTINV_Pos)            /* (ADC_EVCTRL) Start Event Invert Enable Mask */
#define ADC_EVCTRL_STARTINV(value)            (ADC_EVCTRL_STARTINV_Msk & (_UINT8_(value) << ADC_EVCTRL_STARTINV_Pos)) /* Assigment of value for STARTINV in the ADC_EVCTRL register */
#define ADC_EVCTRL_RESRDYEO_Pos               _UINT8_(4)                                           /* (ADC_EVCTRL) Result Ready Event Out Position */
#define ADC_EVCTRL_RESRDYEO_Msk               (_UINT8_(0x1) << ADC_EVCTRL_RESRDYEO_Pos)            /* (ADC_EVCTRL) Result Ready Event Out Mask */
#define ADC_EVCTRL_RESRDYEO(value)            (ADC_EVCTRL_RESRDYEO_Msk & (_UINT8_(value) << ADC_EVCTRL_RESRDYEO_Pos)) /* Assigment of value for RESRDYEO in the ADC_EVCTRL register */
#define ADC_EVCTRL_WINMONEO_Pos               _UINT8_(5)                                           /* (ADC_EVCTRL) Window Monitor Event Out Position */
#define ADC_EVCTRL_WINMONEO_Msk               (_UINT8_(0x1) << ADC_EVCTRL_WINMONEO_Pos)            /* (ADC_EVCTRL) Window Monitor Event Out Mask */
#define ADC_EVCTRL_WINMONEO(value)            (ADC_EVCTRL_WINMONEO_Msk & (_UINT8_(value) << ADC_EVCTRL_WINMONEO_Pos)) /* Assigment of value for WINMONEO in the ADC_EVCTRL register */
#define ADC_EVCTRL_Msk                        _UINT8_(0x3F)                                        /* (ADC_EVCTRL) Register Mask  */


/* -------- ADC_INTENCLR : (ADC Offset: 0x04) (R/W 8) Interrupt Enable Clear -------- */
#define ADC_INTENCLR_RESETVALUE               _UINT8_(0x00)                                        /*  (ADC_INTENCLR) Interrupt Enable Clear  Reset Value */

#define ADC_INTENCLR_RESRDY_Pos               _UINT8_(0)                                           /* (ADC_INTENCLR) Result Ready Interrupt Disable Position */
#define ADC_INTENCLR_RESRDY_Msk               (_UINT8_(0x1) << ADC_INTENCLR_RESRDY_Pos)            /* (ADC_INTENCLR) Result Ready Interrupt Disable Mask */
#define ADC_INTENCLR_RESRDY(value)            (ADC_INTENCLR_RESRDY_Msk & (_UINT8_(value) << ADC_INTENCLR_RESRDY_Pos)) /* Assigment of value for RESRDY in the ADC_INTENCLR register */
#define ADC_INTENCLR_OVERRUN_Pos              _UINT8_(1)                                           /* (ADC_INTENCLR) Overrun Interrupt Disable Position */
#define ADC_INTENCLR_OVERRUN_Msk              (_UINT8_(0x1) << ADC_INTENCLR_OVERRUN_Pos)           /* (ADC_INTENCLR) Overrun Interrupt Disable Mask */
#define ADC_INTENCLR_OVERRUN(value)           (ADC_INTENCLR_OVERRUN_Msk & (_UINT8_(value) << ADC_INTENCLR_OVERRUN_Pos)) /* Assigment of value for OVERRUN in the ADC_INTENCLR register */
#define ADC_INTENCLR_WINMON_Pos               _UINT8_(2)                                           /* (ADC_INTENCLR) Window Monitor Interrupt Disable Position */
#define ADC_INTENCLR_WINMON_Msk               (_UINT8_(0x1) << ADC_INTENCLR_WINMON_Pos)            /* (ADC_INTENCLR) Window Monitor Interrupt Disable Mask */
#define ADC_INTENCLR_WINMON(value)            (ADC_INTENCLR_WINMON_Msk & (_UINT8_(value) << ADC_INTENCLR_WINMON_Pos)) /* Assigment of value for WINMON in the ADC_INTENCLR register */
#define ADC_INTENCLR_Msk                      _UINT8_(0x07)                                        /* (ADC_INTENCLR) Register Mask  */


/* -------- ADC_INTENSET : (ADC Offset: 0x05) (R/W 8) Interrupt Enable Set -------- */
#define ADC_INTENSET_RESETVALUE               _UINT8_(0x00)                                        /*  (ADC_INTENSET) Interrupt Enable Set  Reset Value */

#define ADC_INTENSET_RESRDY_Pos               _UINT8_(0)                                           /* (ADC_INTENSET) Result Ready Interrupt Enable Position */
#define ADC_INTENSET_RESRDY_Msk               (_UINT8_(0x1) << ADC_INTENSET_RESRDY_Pos)            /* (ADC_INTENSET) Result Ready Interrupt Enable Mask */
#define ADC_INTENSET_RESRDY(value)            (ADC_INTENSET_RESRDY_Msk & (_UINT8_(value) << ADC_INTENSET_RESRDY_Pos)) /* Assigment of value for RESRDY in the ADC_INTENSET register */
#define ADC_INTENSET_OVERRUN_Pos              _UINT8_(1)                                           /* (ADC_INTENSET) Overrun Interrupt Enable Position */
#define ADC_INTENSET_OVERRUN_Msk              (_UINT8_(0x1) << ADC_INTENSET_OVERRUN_Pos)           /* (ADC_INTENSET) Overrun Interrupt Enable Mask */
#define ADC_INTENSET_OVERRUN(value)           (ADC_INTENSET_OVERRUN_Msk & (_UINT8_(value) << ADC_INTENSET_OVERRUN_Pos)) /* Assigment of value for OVERRUN in the ADC_INTENSET register */
#define ADC_INTENSET_WINMON_Pos               _UINT8_(2)                                           /* (ADC_INTENSET) Window Monitor Interrupt Enable Position */
#define ADC_INTENSET_WINMON_Msk               (_UINT8_(0x1) << ADC_INTENSET_WINMON_Pos)            /* (ADC_INTENSET) Window Monitor Interrupt Enable Mask */
#define ADC_INTENSET_WINMON(value)            (ADC_INTENSET_WINMON_Msk & (_UINT8_(value) << ADC_INTENSET_WINMON_Pos)) /* Assigment of value for WINMON in the ADC_INTENSET register */
#define ADC_INTENSET_Msk                      _UINT8_(0x07)                                        /* (ADC_INTENSET) Register Mask  */


/* -------- ADC_INTFLAG : (ADC Offset: 0x06) (R/W 8) Interrupt Flag Status and Clear -------- */
#define ADC_INTFLAG_RESETVALUE                _UINT8_(0x00)                                        /*  (ADC_INTFLAG) Interrupt Flag Status and Clear  Reset Value */

#define ADC_INTFLAG_RESRDY_Pos                _UINT8_(0)                                           /* (ADC_INTFLAG) Result Ready Interrupt Flag Position */
#define ADC_INTFLAG_RESRDY_Msk                (_UINT8_(0x1) << ADC_INTFLAG_RESRDY_Pos)             /* (ADC_INTFLAG) Result Ready Interrupt Flag Mask */
#define ADC_INTFLAG_RESRDY(value)             (ADC_INTFLAG_RESRDY_Msk & (_UINT8_(value) << ADC_INTFLAG_RESRDY_Pos)) /* Assigment of value for RESRDY in the ADC_INTFLAG register */
#define ADC_INTFLAG_OVERRUN_Pos               _UINT8_(1)                                           /* (ADC_INTFLAG) Overrun Interrupt Flag Position */
#define ADC_INTFLAG_OVERRUN_Msk               (_UINT8_(0x1) << ADC_INTFLAG_OVERRUN_Pos)            /* (ADC_INTFLAG) Overrun Interrupt Flag Mask */
#define ADC_INTFLAG_OVERRUN(value)            (ADC_INTFLAG_OVERRUN_Msk & (_UINT8_(value) << ADC_INTFLAG_OVERRUN_Pos)) /* Assigment of value for OVERRUN in the ADC_INTFLAG register */
#define ADC_INTFLAG_WINMON_Pos                _UINT8_(2)                                           /* (ADC_INTFLAG) Window Monitor Interrupt Flag Position */
#define ADC_INTFLAG_WINMON_Msk                (_UINT8_(0x1) << ADC_INTFLAG_WINMON_Pos)             /* (ADC_INTFLAG) Window Monitor Interrupt Flag Mask */
#define ADC_INTFLAG_WINMON(value)             (ADC_INTFLAG_WINMON_Msk & (_UINT8_(value) << ADC_INTFLAG_WINMON_Pos)) /* Assigment of value for WINMON in the ADC_INTFLAG register */
#define ADC_INTFLAG_Msk                       _UINT8_(0x07)                                        /* (ADC_INTFLAG) Register Mask  */


/* -------- ADC_SEQSTATUS : (ADC Offset: 0x07) ( R/ 8) Sequence Status -------- */
#define ADC_SEQSTATUS_RESETVALUE              _UINT8_(0x00)                                        /*  (ADC_SEQSTATUS) Sequence Status  Reset Value */

#define ADC_SEQSTATUS_SEQSTATE_Pos            _UINT8_(0)                                           /* (ADC_SEQSTATUS) Sequence State Position */
#define ADC_SEQSTATUS_SEQSTATE_Msk            (_UINT8_(0x1F) << ADC_SEQSTATUS_SEQSTATE_Pos)        /* (ADC_SEQSTATUS) Sequence State Mask */
#define ADC_SEQSTATUS_SEQSTATE(value)         (ADC_SEQSTATUS_SEQSTATE_Msk & (_UINT8_(value) << ADC_SEQSTATUS_SEQSTATE_Pos)) /* Assigment of value for SEQSTATE in the ADC_SEQSTATUS register */
#define ADC_SEQSTATUS_SEQBUSY_Pos             _UINT8_(7)                                           /* (ADC_SEQSTATUS) Sequence Busy Position */
#define ADC_SEQSTATUS_SEQBUSY_Msk             (_UINT8_(0x1) << ADC_SEQSTATUS_SEQBUSY_Pos)          /* (ADC_SEQSTATUS) Sequence Busy Mask */
#define ADC_SEQSTATUS_SEQBUSY(value)          (ADC_SEQSTATUS_SEQBUSY_Msk & (_UINT8_(value) << ADC_SEQSTATUS_SEQBUSY_Pos)) /* Assigment of value for SEQBUSY in the ADC_SEQSTATUS register */
#define ADC_SEQSTATUS_Msk                     _UINT8_(0x9F)                                        /* (ADC_SEQSTATUS) Register Mask  */


/* -------- ADC_INPUTCTRL : (ADC Offset: 0x08) (R/W 16) Input Control -------- */
#define ADC_INPUTCTRL_RESETVALUE              _UINT16_(0x00)                                       /*  (ADC_INPUTCTRL) Input Control  Reset Value */
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
