ice458/RPN_Scientific_Calc/src/decimal_float.c

#include "decimal_float.h"
#include "precomputed_reciprocal_values.h"

// 整数の累乗
int16_t pow_int(int16_t x, int16_t n)
{
    int16_t result = 1;
    for (int16_t i = 0; i < n; i++)
    {
        result *= x;
    }
    return result;
}

// エラーコード生成
void df_error(df_t *a)
{
    a->sign = 1;
    a->exponent = 0;
    for (int8_t i = 0; i < DECIMAL_FLOAT_MANTISSA_SIZE; i++)
    {
        a->mantissa[i] = 0;
    }
}

// 交換
void df_swap(df_t *a, df_t *b)
{
    df_t tmp = *a;
    *a = *b;
    *b = tmp;
}

// 浮動小数点数から10進浮動小数点数への変換
void double_to_df(double f, df_t *a)
{
    if (f == 0)
    {
        a->sign = 0;
        a->exponent = 0;
        for (int8_t i = 0; i < DECIMAL_FLOAT_MANTISSA_SIZE; i++)
        {
            a->mantissa[i] = 0;
        }
        return;
    }

    a->sign = f < 0 ? 1 : 0;
    f = f < 0 ? -f : f;
    a->exponent = 0;

    while (f >= 10)
    {
        f /= 10;
        a->exponent++;
    }
    while (0 < f && f < 1)
    {
        f *= 10;
        a->exponent--;
    }

    for (int8_t i = DECIMAL_FLOAT_MANTISSA_SIZE - 1; i >= 0; i--)
    {
        a->mantissa[i] = (uint8_t)f;
        f = (f - a->mantissa[i]) * 10;
    }
}

// 整数から10進浮動小数点数への変換
void int_to_df(int16_t value, df_t *df)
{
    if (value < 0)
    {
        df->sign = 1;
        value = -value;
    }
    else if (value == 0)
    {
        df->sign = 0;
        df->exponent = 0;
        for (int8_t i = 0; i < DECIMAL_FLOAT_MANTISSA_SIZE; i++)
        {
            df->mantissa[i] = 0;
        }
        return;
    }
    else
    {
        df->sign = 0;
    }

    int16_t temp_value = value;
    int8_t digit_count = 0;

    while (temp_value > 0)
    {
        digit_count++;
        temp_value /= 10;
    }

    df->exponent = digit_count - 1;

    for (int8_t i = 0; i < DECIMAL_FLOAT_MANTISSA_SIZE - digit_count + 1; i++)
    {
        df->mantissa[i] = 0;
    }
    for (int8_t i = DECIMAL_FLOAT_MANTISSA_SIZE - digit_count; i < DECIMAL_FLOAT_MANTISSA_SIZE; i++)
    {
        df->mantissa[i] = value % 10;
        value /= 10;
    }
}
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
